thomasf10/cosy_cafeteria/Report/Onderzoek op sensoren.docx

# Eerste testen op de CCS811

- Eerste test: meting op 60 sec => meting niet meteen na slaap beschikbaar.
- Tweede test metingen 250 ms en 1s => me chronometer gechronometreerd ongeveer 1 second tussen elke meting. Verder nauwkeuriger onderzoek nodig. Tijd van de meting zelf niet de tijd tussen weergaven.
- Derde test 10 SEC => Eerste meting duurt precies langer dan de daarop volgende die zijn mooi consistent om de 10 seconden.
- Vierde test opmeten van 250ms => Eerst meting duurt ongeveer 940ms na uit slaap. Vanaf daarna effectief om de 250 ms een meting. => Dit is zeer consistent.

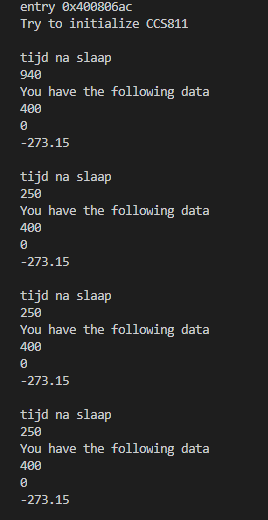
[picture p29: figure]

- Vijfde test 1 second nauwkeurig meten. Zelfde resultaat van eerste meting trager en volgende meting om de 250ms. Een meting mogelijk. Dit is achter elke meting dus. Eerste keer duurt het wel heel lang. Dit komt meteen achter initialisatie. Dus misschien intensiteit meting intensiever bij 250ms. Straks datasheet vermogen verbruik en uitleg bekijken.

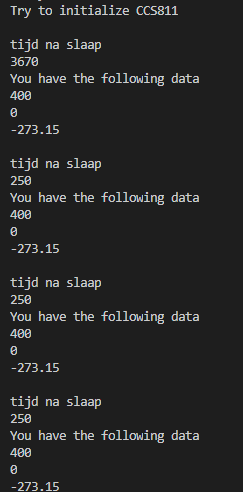
[picture p30: figure]

- Zesde test wat bij 10 seconden meting duurt dan ook 250ms? Antwoord nee, de meting duurt nu veel langer zelf 8,12 seconden. Meting snelheid 250ms en 1s zelfde maar interval tussen elke meting is verschillend. 250ms sneller inzetbaar na initialisatie of (lange slaap?).

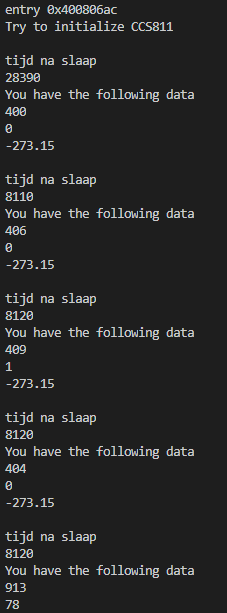
[picture p31: figure]

- Indien CCS811 vanuit idle wordt gestart duurt het altijd lang? Antwoor dis éénduidig ja, zowle voor de 250ms als voor de 1s. Dus dat omzetten van meetmethode kost extra tijd ook al komt hij uit idle. Beter gewoon in en uitslaap brengen werkt zeer snel enz al minder aan tijd kosten voor sensor basis verbruik. Ik zou ook opteren voor de 250msec in plaats van de 1s sneller een eerst resultaat waarschijnlijk na lange uitstand en dus ook sneller af zetten mogelijk. Verbruik is dezelfde bij beide. Tijdens de 250ms kunnen we effectief ook een andere meting / instelling doen van andere elementen.

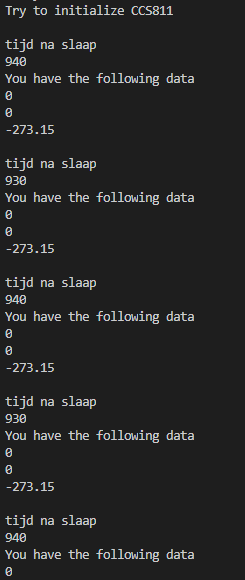
[picture p32: figure]

Bij effect van de snelle mode over een ganse minuut bekeken is bij continue meer verbruik maar dat zal gedurende 1 minuut zijn want dan voer je constant metingen uit en voed je de sensor continue. Bij deze impuls methode veel minder en dus sneller voeding afzetten. 1 ding nog testen op school. Is het verbruik komt dit wel ten goede is er een opstart stroompiek of niet?

Wat als we naar realistische verspreiding van metingen gaan.

- Meting om de 5 minuten:

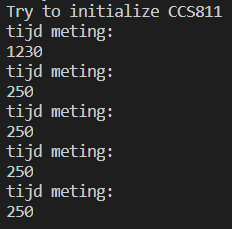
[picture p33: figure]

- Meting om het uur:

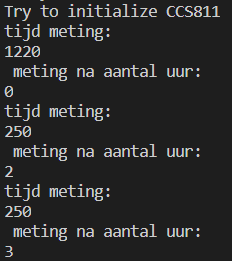
[picture p34: figure]

Indeed after a sleep time of 1hour the respons of the sensor is 250 ms.

Dus we kunnen eigenlijk deze tijd ook nuttig gebruiken we weten na 250ms na de CCS811 uit slaap te brengen dat hij een meting klaar heeft staan.

Mijn idee als dit ook bij de AMG zo is, zou ik een functie schrijven die eerst de traagste sensor activeert en dan de rest. Vanaf er een sensor data heeft die al uitlezen en weer in slaapbrengen. Enzo elke sensor afgaan tot we ze allemaal hebben uitgelezen en meteen in slaapgezet of voeding uit. Nu voor de CCS811 raad ik het afomdat zoals je ziet hij waarschijnlijk moet eerts geinitaliseerd worden en dan zijn eerste meting altijd toch wel 4x langer duurt.

# Gezamelijke testen op de AMG8833

Dit is het meest snelle resultaat, dit is vantoepassing indien we elke pixal van de AMG8833 sensor zouden uitmeten. Waarom eerst AMG dan CCS => CCS zakl pas na 250ms een resultaat hebben de AMG al na 105. Als de meting klaar is, kan je meteen de CCS uitlezen. Na de wake fucntie zal een delay van 105ms moeten gekozen worden. Ik ga ook nog de ADC er proberen in te steken en bekijken wat dan delays worden.

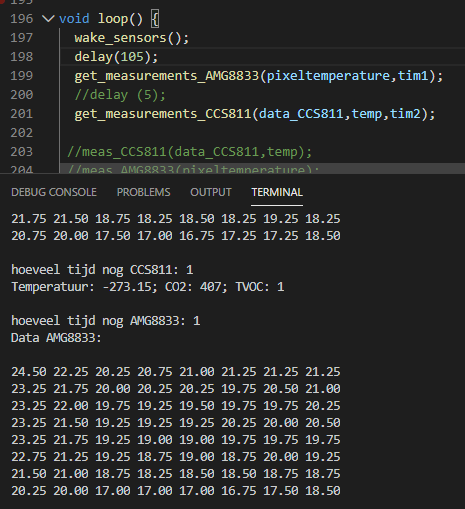
[picture p35: figure]

Na de ADC zal ik nog met de greco verbruiksmetingen doen en dan is dit verslag compleet.

The ADC was added, the ADC measurement did not introduced an extra delay. So, after the wake and ADC result there is a timeframe of 105 ms that we must wait for data of the AMG8833 and the CCS811 that will be even later available.

# Persoon detectie testen

## Hoogte 3,4m koude ruimte

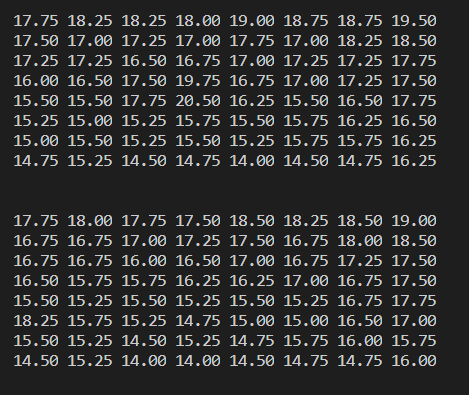
[picture p36: figure]

D

ZIe ook Excel, daarin zie je dat als de sensor op 3,4 meter hoog is een persoon door 1 à 2 pixels te Sherkenen en ligt in graden celcius drie graden hoger dan niet. Dit is wel in een koudere ruimte gebeurd zie vooral de temperaturen die zijn effectief zo laag.

Even nog een berekening doen checken of dat klopt. Verschil in hoogte is 1,6 m want ik ben zelf 1,8m ongeveer. Dus beetje geometrie nu doen.

30°

? m

1,7 m

tan 30°=(overstaande)/(aanliggende)=>overstaande=aanliggende∙tan30 °=1,6 m∙0,577=0,924m

Dit over vier pixels verspreid => 0,23 meter.

1 http://www.dinbelg.be/volwassenentotaal.htm

2 https://ohsonline.com/Articles/2008/01/Study-Womens-Skulls-Thicker-Mens-Wider-Might-Affect-Protection-Design.aspx

Dit is een tweede bron

Dus dit kan inderdaad wel goed kloppen. Weet ook we geven vooral langs ons hoofd veel warmte af als we ons kleden dus.

Bekijk ook het csv-bestand ‘Person tracking’. Daar zie me getracked worden door de de AMG sensor. Ik zette meestal ongeveer een halve meter een stap zijwaarts of voor-/achterwaards. Dus dat komt precies wel mooi uit met de resultaten.

## Metingen verschillende elementen

Eerst blok is op het hoofd gericht, tweede is borst met een dikke trui en tot slot iets van de omgeving. Dit laatste is wel op een meter afstand maar het is wel een goede represetatie van de warmte in de ruimte.

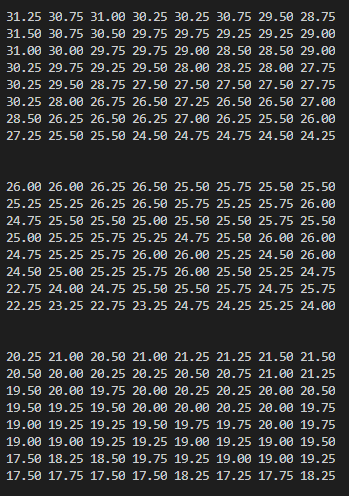
[picture p37: figure]

Laatste onderzoek is het verbruik nog, dit zal eerder voor volgend weekend zijn, denk ik.
