thomasf10/cosy_cafeteria/presentation/tussentijdsepresentatie.pptx

## Embedded 2 – Cosy cafetaria Corona presentation

By Tobias Cromheecke, Thomas Feys, Robin Van de Poel, Arthur Van den Storme
16-4-2020

## Index

- Power management
- Microcontroller + main PCB
- Sensor design
- Housing design
- Software design
- Wi-Fi communication
- Dashboard

## Power management

- Completed:

- Battery: Lithium-Ion battery
- Charger IC
- Protection IC
- Reverse polarity protection circtuit
- LDO: 3,7 V to 3,3 V
- Load switches to turn on/off the sensors
- Availability to measure current via wire to put a currentprobe on or sense resistor

- To do:

- Soldering
- Testing
- Designing revision

## Problems/limitations

- Delay times for deliveries due corona measures
- Lack of tools/instruments to solder and for testing:
  - Most power management IC’s have an exposed pad which needs a solder oven to solder properly
  - Lack of oscilloscope etc.

## Microcontroller + main PCB

- Completed:

- ESP32 single core
- Design main pcb
- Boot and reset button

- To do:

- Soldering
- Testing
- Designing revision

## Sensor design

- Completed:

- PCB design of separate sensor board
- Investigating response time of sensors
- Bringing sensors
  - Functions: init, get data, sleep,…

- To do:

- Power measurements
  - Checking measure mode is the most efficient
  - Checking with a Gecko development board

## Problems/limitations

- Correct cooperation of sensor board with the main board.

## Housing design

- Completed:

- Discussing a basic idea of the housing
- Getting the measurements of all available part
- A tutorial on 3D-printing design with fusion360

- To do:

- Design of the housing taken all the individual elements into account

## Problems/limitations

- Available 3D-printer
  - Do not own one
  - 3D-printer at work, could be a possibility Need to check with work
- Checking the fitting of the design in the housing

## Software design

- Completed:

- Entering and wakeup from deep sleep
- Save variables in RTC memory so that they are retained after deep sleep
- NTP synchronisation for time information => disable sensors at night

- To do:

- Put the individual pieces of software in one general structure
- Test the system
- Power measurements

## Problems/limitations

- No ability to fully disable sensors with load switch until the final PCB is ready
- No ability to measure power consumption
- Difficult to test full system because sensors, Raspberry Pi and ESP32-SOLO are not all available to one person

## Wi-Fi communication

- Completed:

- Data transfer between ESP32 and Python server
- Faster connection setup because of static IP => reduced power consumption

- To do:

- Process received data in Python
- Measure power consumption
- Test connection with actual sensor data instead of dummy data
- Test Python server on Raspberry Pi instead of laptop

## Dashboard

- Completed:

- Basic functionality for 1 type
- Data base design
- Data base implementation
- Functional heatmap

- To do:

- Test on raspberry pi
- Use real sensor data
- Make it look good
- Add the other sensors
- Main page
