thomasf10/cosy_cafeteria/Sensors/IR_Sensor_Embedded_Design_1_Verslag_Jona_Cappelle_Thomas_Feys.pdf

# Lab: Embedded system design 1

Thomas Feys | Jona Cappelle

16 december 2019

1

## Inhoudsopgave

1 Inleiding | 3
2 Sensor | 3
3 Systeem | 5
4 Code | 6
5 Power consumptie | 7
6 Besluit | 10
7 Bijlage | 11

2

## 1 Inleiding

Ons doel is om de wachtrij in de rabotaria te monitoren. Dit zullen we doen aan de hand van een IR grid sensor (AMG8833). Aan de hand van de uitgelezen waarden zullen we in het tweede semester bepalen hoeveel mensen er in de wachtrij staan. Deze informatie zullen we vervolgens via een app of website verspreiden.

## 2 Sensor

De sensor die we gebruiken om de wachtrij te monitoren is de AMG8833. Deze IR grid sensor heeft 8x8 pixels die de temperatuur weergeven. Volgens de datasheet kan a.d.h.v. de temperatuur een mens waargenomen worden vanop een afstand van 5 meter. De sensor kan gebruikt worden in 3 verschillende modes: normal, sleep en stand-by. In de normale mode heeft de sensor een verbruik van 4.5 mA. De stand-by mode heeft twee opties; de waardes kunnen geupdatet worden om de 60 ¨ seconden of om de 10 seconden. In deze mode is er een verbruik van 0.8 mA. Als laatste is er de sleep mode deze verbruikt 0.2 mA. Een overzicht van alle modes en de commando’s die verstuurd moeten worden om in deze modes te gaan, wordt weergegeven in figuur 1. Tijdens het testen van de sensor hebben we periodiek geswitched tussen de verschillende power modes. Het resultaat van deze test is te zien in figuur 2. De sensor heeft ook een interrupt pin. Deze pin geneert een interrupt als een van de pixels over of onder een bepaalde waarde gaat. Deze waarde is instelbaar.

3

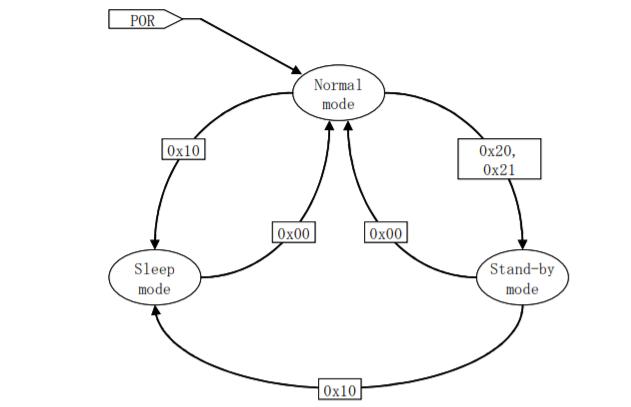
[picture p80: figure]

Figuur 1: Overzicht operating modes

4

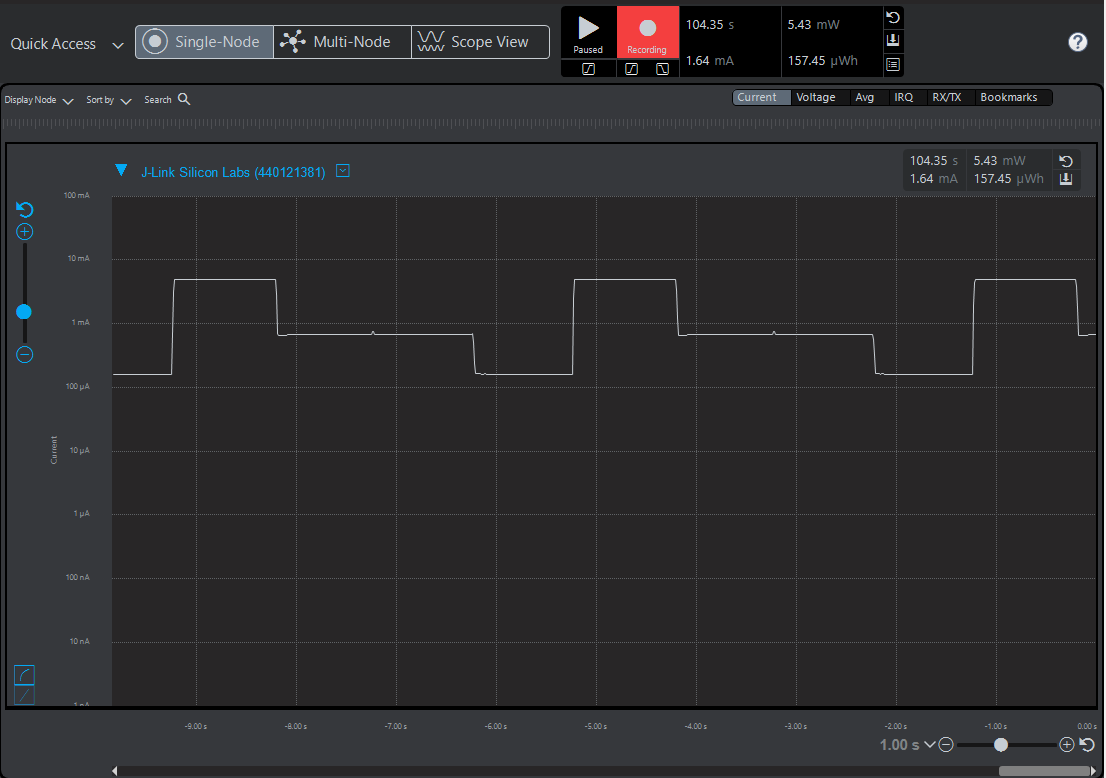
[picture p81: figure]

Figuur 2: Test van de verschillende powermodes

## 3 Systeem

### 3.1 Overzicht

De AMG8833 communiceert met de EFM32 via I2C. Naast de I2C communicatie is er ook een interrupt pin voorzien op de sensor. Deze pin genereert een interrupt als er een van de pixels een bepaalde, instelbare waarde overschrijdt. Een volledig overzicht van het systeem is te zien in figuur 3.

5

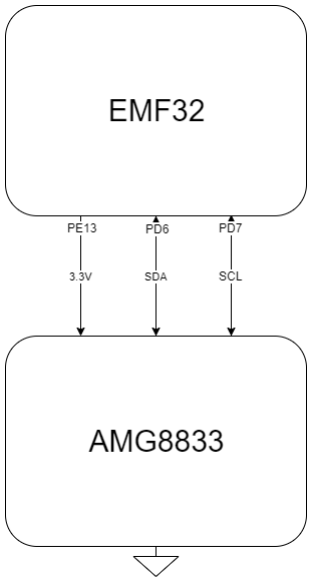
[picture p82: figure]

Figuur 3: Overzicht van het systeem

### 3.2 I2C

De communicatie met de sensor gebeurt via I2C. Het adres van de sensor is een 7 bit adres namelijk: 1101001. Aangezien we met een 7 bit adres zitten moet deze 1 bit geshift worden naar links. Dit adres moet telkens naar de sensor verstuurd worden vooraleer er iets gelezen of geschreven kan worden. De code die gebruikt wordt om de sensor uit te lezen, in andere powermodus te zetten en te interrupten wordt in de volgende sectie besproken.

## 4 Code

### 4.1 Functionaliteiten

Om gemakkelijk met de sensor te werken werd er een library geschreven voor de AMG8833. Er werden verschillende methodes geschreven om vlot te kunnen omgaan met de sensor. Er werd een functie geschreven om alle pixels uit te lezen. Naast de pixels is er ook een thermistor aanwezig in de sensor, ook hiervoor werd een functie geschreven. Er werden ook verschillende functies geschreven om makkelijk tussen de verschillende powermodes te kunnen wisselen. Een volledig overzicht van deze library en de rest van de code is terug te vinden op github: https://github.com/jonacappelle/Embedded_Project of in hoofdstuk 7.

6

### 4.2 Flow van de code

Aangezien de sensor in stand-by een verbruik van 0.8 mA heeft wordt deze altijd in sleep gezet. De sensor wordt om de 5 minuten uit sleep gehaald om alle pixels uit te lezen. Hierna wordt ze weer in sleep gezet. Een volledig overzicht van de code is terug te vinden in figuur 4.

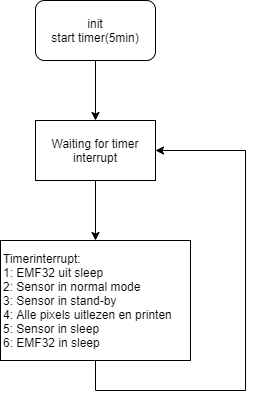
[picture p83: figure]

Figuur 4: flowchart van de code

## 5 Power consumptie

### 5.1 Sensor

De sensor heeft 3 verschillende powermodes, deze zijn te zien in figuur 5. Deze hebben we ook zelf opgemeten zoals te zien is in figuur 2. De gemeten waarden liggen in dezelfde grote orde als deze die opgegeven zijn in de datasheet, maar wijken toch een klein beetje af. In normal mode gebruikt onze sensor 4.95 mA, in stand-by 0.66 mA en in sleep 0.156 mA.

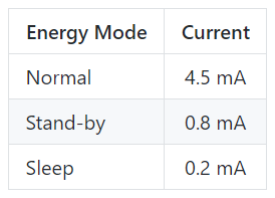
[picture p84: figure]

Figuur 5: powermodes van de sensor

7

### 5.2 Principe

Door de methode toe te passen die besproken werd in section 4.2 wordt de power consumptie sterk verminderd. De sensor zit enkel in stand-by tijdens het uilezen van de sensor waarde. De sensor zit ook 105 ms in normal mode, omdat je altijd naar de normal mode moet gaan als je uit sleep komt. Er werd een meting uitgevoerd om dit verbruik te controleren, dit is terug te vinden in figuur 6. Uit deze meting is te zien dat de sensor 105 ms in normal mode zit met een verbruik van 4.8 mA, 50ms in stand-by met een verbruik van 2.83 mA¹
en verder zit de sensor in sleep met een verbruik van 0.156 mA. Hierdoor bekomen we volgend verbruik per meting:

3.3 V ·

105 ms · 4.8 mA + 50 ms · 2.83 mA + 299.845 s · 0.156 mA = 156.4904 mJ/meting (1)

Een overzicht is te zien in tabel 1.

Power Mode | Verbruik [mA] | Tijd [s] | Energie [mJ]
Normal | 4.8 | 0.105 | 1.6632
Stand-By | 2.83 | 50 | 0.4669
Sleep | 0.156 | 299.845 | 154.3602
| | Totaal | 156.4904

Tabel 1: Verbruik voor ´e´en meting

Als we om de 5 minuten een meting uitvoeren, bekomen we volgend verbruik:

12 · 156.4904 mJ
| meting

= 1.877 mJ

| ⇒ 1.877 J
| 3600 s

= 0.52 mW

1Tijdens het uitlezen van de sensor ligt het verbruik hoger, hierdoor verbruikt de sensor 2.83 mA in stand-by ipv 0.8 mA

8

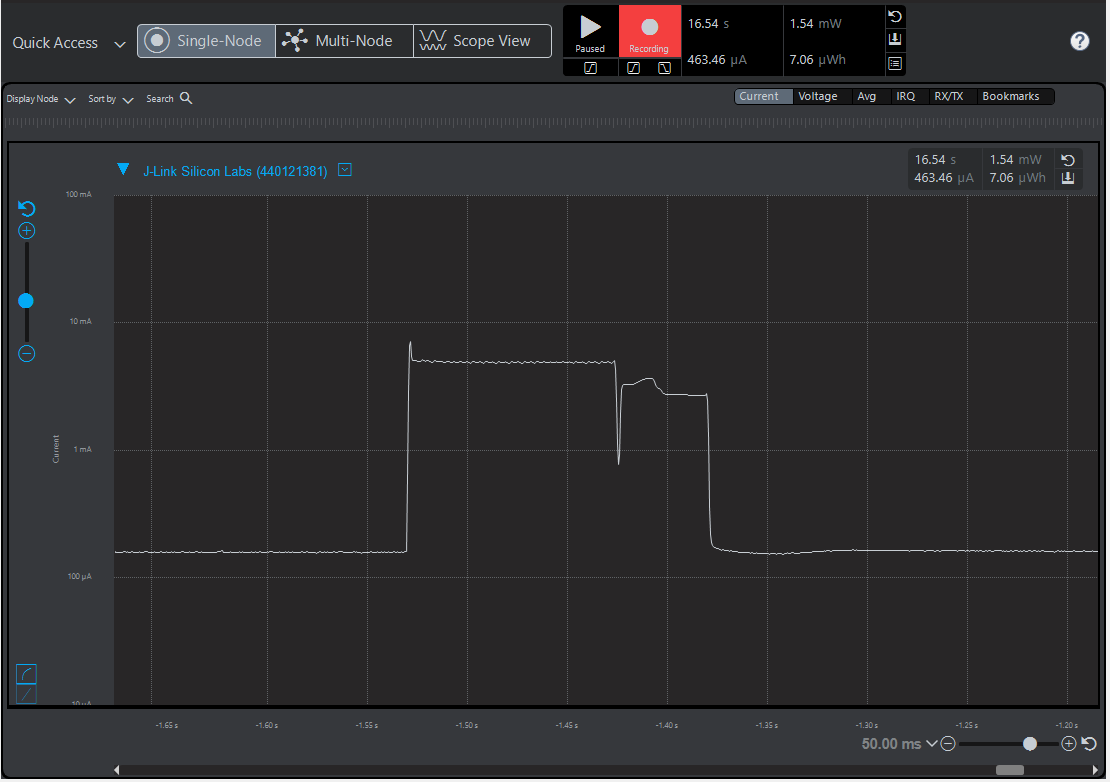
[picture p85: figure]

Figuur 6: Meting verbruik

9

## 6 Besluit

In dit labo hebben we een grid eye sensor aangesproken aan de hand van een I2C verbinding. Er werd een library geschreven om te werken met de verschillende functionaliteiten van de sensor. Deze library werd vervolgens gebruikt om de sensor op een low power manier te gebruiken. Dit leverde uiteindelijk een verbruik van 0.52 mW op.

10

## 7 Bijlage

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

44
45 | f l o a t r B u f f e r T h e rmi s t o r [ 1 ] ;
46 | f l o a t r B u f f e r P i x e l s [ 6 4 ] ;
47
48 | v o l a t i l e u i n t 3 2 t msTickCount ; | /∗ Counts 1ms t ime t i c k s ∗/
49 | s t a t i c v o l a t i l e u i n t 3 2 t msTicks ; /∗ c o u n t s 1ms t imeT ick s ∗/
50
51
52 | /∗ ∗∗∗∗∗∗∗∗∗∗∗∗∗∗∗∗∗∗∗∗∗∗∗∗∗∗∗∗∗∗∗∗∗∗∗∗∗∗∗∗∗∗∗∗∗∗∗∗∗∗∗∗∗∗∗∗∗∗∗∗∗∗∗∗∗∗∗∗∗∗∗∗ ∗/ /∗ ∗
53 | ∗ @ b r i e f
54 | ∗ | Sy sT ick H an dle r needed f o r t ime r f u n c t i o n a l i t y
55 | ∗
56 | ∗∗∗∗∗∗∗∗∗∗∗∗∗∗∗∗∗∗∗∗∗∗∗∗∗∗∗∗∗∗∗∗∗∗∗∗∗∗∗∗∗∗∗∗∗∗∗∗∗∗∗∗∗∗∗∗∗∗∗∗∗∗∗∗∗∗∗∗∗∗∗∗∗∗∗∗ ∗/
57 | void S y sTic k H andle r ( void )
58 | {
59 | msTicks++; | /∗ incremen t c o u n t e r n e c e s s a r y in Delay ( ) ∗/
60 | }
61
62 | /∗ ∗∗∗∗∗∗∗∗∗∗∗∗∗∗∗∗∗∗∗∗∗∗∗∗∗∗∗∗∗∗∗∗∗∗∗∗∗∗∗∗∗∗∗∗∗∗∗∗∗∗∗∗∗∗∗∗∗∗∗∗∗∗∗∗∗∗∗∗∗∗∗∗ ∗/ /∗ ∗
63 | ∗ @ b r i e f S y s T i c k D i s a b l e
64 | ∗ D i s a b l e s y s t i c k i n t e r r u p t s
65 | ∗∗∗∗∗∗∗∗∗∗∗∗∗∗∗∗∗∗∗∗∗∗∗∗∗∗∗∗∗∗∗∗∗∗∗∗∗∗∗∗∗∗∗∗∗∗∗∗∗∗∗∗∗∗∗∗∗∗∗∗∗∗∗∗∗∗∗∗∗∗∗∗∗∗∗∗ ∗/
66 | s t a t i c void S y sTi c kDi s a bl e ( void )
67 | {
68 | SysTick−>CTRL = 0 x0000000 ;
69 | }
70
71 | /∗ ∗∗∗∗∗∗∗∗∗∗∗∗∗∗∗∗∗∗∗∗∗∗∗∗∗∗∗∗∗∗∗∗∗∗∗∗∗∗∗∗∗∗∗∗∗∗∗∗∗∗∗∗∗∗∗∗∗∗∗∗∗∗∗∗∗∗∗∗∗∗∗∗ ∗/ /∗ ∗
72 | ∗ @ b r i e f
73 | ∗ | C on f ig u re t h e SysT ick t o use cmuClock CORE f o r 1 ms i n t e r r u p t s
74 | ∗
75 | ∗∗∗∗∗∗∗∗∗∗∗∗∗∗∗∗∗∗∗∗∗∗∗∗∗∗∗∗∗∗∗∗∗∗∗∗∗∗∗∗∗∗∗∗∗∗∗∗∗∗∗∗∗∗∗∗∗∗∗∗∗∗∗∗∗∗∗∗∗∗∗∗∗∗∗∗ ∗/
76 | void d e l a y i n i t ( void )
77 | {
78 | /∗ Se tup SysT ick Timer f o r 1 msec i n t e r r u p t s | ∗/
79 | i f ( S y sTi c k C o n fi g ( CMU ClockFreqGet ( cmuClock CORE ) / 1 0 0 0 ) ) {
80 | while ( 1 ) ;
81 | }
82 | }
83
84 | /∗ ∗∗∗∗∗∗∗∗∗∗∗∗∗∗∗∗∗∗∗∗∗∗∗∗∗∗∗∗∗∗∗∗∗∗∗∗∗∗∗∗∗∗∗∗∗∗∗∗∗∗∗∗∗∗∗∗∗∗∗∗∗∗∗∗∗∗∗∗∗∗∗∗ ∗/ /∗ ∗
85 | ∗ @ b r i e f
86 | ∗ | Non−low−power del ay , b u t non−b l o c k i n g
87 | ∗
88 | ∗ @param [ in ] d l y T i c k s
89 | ∗ | How many m i l l i sec on d s d e l a y

12

90 | ∗
91 | ∗∗∗∗∗∗∗∗∗∗∗∗∗∗∗∗∗∗∗∗∗∗∗∗∗∗∗∗∗∗∗∗∗∗∗∗∗∗∗∗∗∗∗∗∗∗∗∗∗∗∗∗∗∗∗∗∗∗∗∗∗∗∗∗∗∗∗∗∗∗∗∗∗∗∗∗ ∗/
92 | void d el a y ( u i n t 3 2 t dl yTi c k s )
93 | {
94 | | u i n t 3 2 t c u rTi c k s ;
95
96 | | c u rTi c k s = msTicks ;
97 | | while ( ( msTicks − c u rTi c k s ) < dl yTi c k s ) ;
98 | }
99
100 | /∗ ∗∗∗∗∗∗∗∗∗∗∗∗∗∗∗∗∗∗∗∗∗∗∗∗∗∗∗∗∗∗∗∗∗∗∗∗∗∗∗∗∗∗∗∗∗∗∗∗∗∗∗∗∗∗∗∗∗∗∗∗∗∗∗∗∗∗∗∗∗∗∗∗ ∗/ /∗ ∗
101 | ∗ @ b r i e f
102 | ∗ | C a l l b a c k f u n c t i o n f o r 5 min t ime r
103 | ∗
104 | ∗∗∗∗∗∗∗∗∗∗∗∗∗∗∗∗∗∗∗∗∗∗∗∗∗∗∗∗∗∗∗∗∗∗∗∗∗∗∗∗∗∗∗∗∗∗∗∗∗∗∗∗∗∗∗∗∗∗∗∗∗∗∗∗∗∗∗∗∗∗∗∗∗∗∗∗ ∗/
105 | void C all b a c k Sl e e p ( void )
106 | {
107 | | appS t a te = MEASURE;
108 | }
109
110
111 | /∗ ∗∗∗∗∗∗∗∗∗∗∗∗∗∗∗∗∗∗∗∗∗∗∗∗∗∗∗∗∗∗∗∗∗∗∗∗∗∗∗∗∗∗∗∗∗∗∗∗∗∗∗∗∗∗∗∗∗∗∗∗∗∗∗∗∗∗∗∗∗∗∗∗ ∗/ /∗ ∗
112 | ∗ @ b r i e f GPIO Even IRQ f o r p u s h b u t t o n s on even−numbered p i n s
113 | ∗∗∗∗∗∗∗∗∗∗∗∗∗∗∗∗∗∗∗∗∗∗∗∗∗∗∗∗∗∗∗∗∗∗∗∗∗∗∗∗∗∗∗∗∗∗∗∗∗∗∗∗∗∗∗∗∗∗∗∗∗∗∗∗∗∗∗∗∗∗∗∗∗∗∗∗ ∗/
114 | void GPIO EVEN IRQHandler ( void )
115 | {
116 | | // Cle a r a l l even p in i n t e r r u p t f l a g s
117 | | GPIO IntClear ( 0 x5555 ) ;
118 | | appS t a te = MEASURE;
119
120 #i f DEBUG DBPRINT == 1 /∗ DEBUG DBPRINT ∗/
121 | | d b p ri n t ( ” I n t e r r u p t f i r e d ! 1 ” ) ;
122 #end i f /∗ DEBUG DBPRINT ∗/
123 }
124
125 | /∗ ∗∗∗∗∗∗∗∗∗∗∗∗∗∗∗∗∗∗∗∗∗∗∗∗∗∗∗∗∗∗∗∗∗∗∗∗∗∗∗∗∗∗∗∗∗∗∗∗∗∗∗∗∗∗∗∗∗∗∗∗∗∗∗∗∗∗∗∗∗∗∗∗ ∗/ /∗ ∗
126 | ∗ @ b r i e f GPIO Odd IRQ f o r p u s h b u t t o n s on odd−numbered p i n s
127 | ∗∗∗∗∗∗∗∗∗∗∗∗∗∗∗∗∗∗∗∗∗∗∗∗∗∗∗∗∗∗∗∗∗∗∗∗∗∗∗∗∗∗∗∗∗∗∗∗∗∗∗∗∗∗∗∗∗∗∗∗∗∗∗∗∗∗∗∗∗∗∗∗∗∗∗∗ ∗/
128 | void GPIO ODD IRQHandler ( void )
129 | {
130 | | // Cle a r a l l odd p in i n t e r r u p t f l a g s
131 | | GPIO IntClear ( 0xAAAA) ;
132 | | appS t a te = MEASURE;
133
134 #i f DEBUG DBPRINT == 1 /∗ DEBUG DBPRINT ∗/
135 | | d b p ri n t ( ” I n t e r r u p t f i r e d ! 2 ” ) ;

13

136 #end i f /∗ DEBUG DBPRINT ∗/
137 }
138
139 | /∗ ∗∗∗∗∗∗∗∗∗∗∗∗∗∗∗∗∗∗∗∗∗∗∗∗∗∗∗∗∗∗∗∗∗∗∗∗∗∗∗∗∗∗∗∗∗∗∗∗∗∗∗∗∗∗∗∗∗∗∗∗∗∗∗∗∗∗∗∗∗∗∗∗ ∗/ /∗ ∗
140 | ∗ @ b r i e f
141 | ∗ | Main f u n c t i o n
142 | ∗
143 | ∗ @ d e t a i l s
144 | ∗ | We used a s t a t e machine t o c o n t r o l t h e s t a t e s where our m i c r o c o n t r o l l e r i s in
145 | ∗
146 | ∗∗∗∗∗∗∗∗∗∗∗∗∗∗∗∗∗∗∗∗∗∗∗∗∗∗∗∗∗∗∗∗∗∗∗∗∗∗∗∗∗∗∗∗∗∗∗∗∗∗∗∗∗∗∗∗∗∗∗∗∗∗∗∗∗∗∗∗∗∗∗∗∗∗∗∗ ∗/
147 | int main ( void )
148 | {
149 | /∗ I n f i n i t e l o o p ∗/
150 | while ( 1 )
151 | {
152 | switch ( appS t a te )
153 | {
154 | case INIT :
155 | {
156 | /∗ Chip e r r a t a ∗/
157 | CH IP Init ( ) ;
158
159 | /∗ Enable GPIO c l o c k s ∗/
160 | CMU ClockEnable ( cmuClock GPIO , t r u e ) ;
161 | CMU ClockEnable ( cmuClock HFPER , t r u e ) ; // Needed t o use GPIO
162 | CMU ClockEnable ( cmuClock CORE , t r u e ) ;
163
164 | /∗ Watchdog s e t u p − Use d e f a u l t s , e x c e p t s f o r t h e s e : ∗/
165 | w I ni t . em2Run = t r u e ;
166 | w I ni t . em3Run = t r u e ;
167 | w I ni t . p e r S el = wdogPeriod 4k ; /∗ 4k 1kHz p e r i o d s s h o ul d g i v e ˜4 | sec on d s in EM3 ∗/
168
169 | /∗ I n i t i a l i z e RTC t ime r . ∗/
170 | RTCDRV Init ( ) ;
171 | RTCDRV AllocateTimer ( &xTimerForWakeUp ) ;
172
173 | /∗ S t a r t I2C ∗/
174 | I I C I n i t ( ) ;
175
176 | /∗ S t a r t AMG8833 Temp s e n s o r ∗/
177 | AMG8833 Init ( ) ;
178
179 | /∗ S t a r t Delay ∗/
180 | d e l a y i n i t ( ) ;
181

14

182 | /∗ Se tup p r i n t i n g t o v i r t u a l COM p o r t ∗/
183 | #i f DEBUG DBPRINT == 1 /∗ DEBUG DBPRINT ∗/
184 | dbp rin t IN IT (USART1, 4 , t rue , f a l s e ) ;
185 | #e n d i f /∗ DEBUG DBPRINT ∗/
186
187 | appS t a te = MEASURE;
188 | } break ;
189 | case MEASURE:
190 | {
191 | /∗ Se t t o StandBy 10 s e c ∗/
192 | AMG8833 Sleep ( f a l s e ) ;
193 | AMG8833 StandBy ( STBY 60 ) ;
194
195 | RTCDRV StartTimer ( xTimerForWakeUp , rtcdrvTimerTypeOneshot , 1 0 5 , NULL, NULL ) ;
196 | EMU EnterEM2 ( t r u e ) ;
197
198 | //AMG8833 Thermistor Read ( r B u f f e r T h e rm i s t o r ) ;
199 | AMG8833 Pixels Read ( r B u f f e r P i x e l s ) ;
200
201 | appS t a te = SLEEP;
202
203 #i f DEBUG DBPRINT == 1 /∗ DEBUG DBPRINT ∗/
204 | AMG8833 Pixel Print ( r B u f f e r P i x e l s ) ;
205 #end i f /∗ DEBUG DBPRINT ∗/
206
207 | appS t a te = SLEEP;
208 | } break ;
209 | case SLEEP:
210 | {
211 | /∗ Sensor t o s l e e p −−> 0 . 2 mA ∗/
212 | AMG8833 Sleep ( t r u e ) ;
213
214 | /∗ EFM t o s l e e p ∗/
215 | S y sTi c kDi s a bl e ( ) ;
216 | RTCDRV StartTimer ( xTimerForWakeUp , rtcdrvTimerTypeOneshot , 5 0 0 0 , | C all b a c k Sl e e p , NULL ) ;
217 | EMU EnterEM2 ( t r u e ) ;
218 | } break ;
219 | }
220 | }
221 | }

15

../Embedded 1 AMG8833 Temp Sensor/AMG8833/AMG8833.h
1 | /∗
2 | ∗ AGM8833 . h
3 | ∗
4 | ∗ | Crea ted on : Nov 18 , 2019
5 | ∗ | Author : j on ac
6 | ∗/
7
8 | /∗ ∗∗∗∗∗∗∗∗∗∗∗∗∗∗∗∗∗∗∗∗∗∗∗∗∗∗∗∗∗∗∗∗∗∗∗∗∗∗∗∗∗∗∗∗∗∗∗∗∗∗∗∗∗∗∗∗∗∗∗∗∗∗∗∗∗∗∗∗∗∗∗∗∗ ∗/ /∗ ∗
9 | ∗ @ f i l e AMG8833 . h
10 | ∗ @ b r i e f I n t e r f a c e w i t h AMG8833 IR Temp camera
11 | ∗ @vers ion 1 . 0
12 | ∗ @author Jona C a p p ell e & Thomas Feys
13 | ∗ ∗∗∗∗∗∗∗∗∗∗∗∗∗∗∗∗∗∗∗∗∗∗∗∗∗∗∗∗∗∗∗∗∗∗∗∗∗∗∗∗∗∗∗∗∗∗∗∗∗∗∗∗∗∗∗∗∗∗∗∗∗∗∗∗∗∗∗∗∗∗∗∗∗∗∗ ∗/
14
15 #i fnd e f AMG8833 H
16 #def ine AMG8833 H
17
18 | /∗ Needed t o use u i n t x t ∗/
19 #include <s t d i n t . h> | /∗ Needed t o use u i n t x t ∗/
20 #include <s t d b o ol . h> | /∗ Needed t o use b o ol e a n s ∗/
21
22 #def ine I2C ADDRESS | ( 0 x69 << 1 ) /∗ MCU works w i t h | 10 b i t I2C a d d r e s s e s , so we need t o s h i f t our a d d r e s s 1 b i t ∗/
23
24 #def ine POWERCONTROL | 0 x00 | /∗ Power c o n t r o l a d d r e s s ∗/
25 #def ine POWERCONTROLNORMAL | 0 x00 | /∗ Power c o n t r o l s e t t o normal mode ∗/
26 #def ine POWER CONTROL SLEEP | 0 x10 | /∗ Power c o n t r o l s e t t o s l e e p mode ∗/
27 #def ine POWER CONTROL STBY 60 | 0 x20 | /∗ Power c o n t r o l s e t t o s t an dby , measure e v e ry 60 s e c ∗/
28 #def ine POWER CONTROL STBY 10 | 0 x21 | /∗ Power c o n t r o l s e t t o s t an dby , measure e v e ry 10 s e c ∗/
29
30 #def ine AMG8833 POWER PORT | gpioPortE | /∗ Power Por t ∗/
31 #def ine AMG8833 POWER PIN | 13 | /∗ Power Pin ∗/
32
33 #def ine AMG8833 INTERRUPT PORT | gpioPortD | /∗ I n t e r r u p t Por t ∗/
34 #def ine AMG8833 INTERRUPT PIN | 4 | /∗ I n t e r r u p t Pin ∗/
35 #def ine AMG8833 INT CONTROL REGISTER | 0 x03 | /∗ I n t e r r u p t c o n t r o l r e g i s t e r ∗/
36 #def ine AMG8833 INT LEVEL REGISTER | 0 x08 | /∗ I n t e r r u p t l e v e l r e g i s t e r ( upper l i m i t ) ∗/
37
38 #def ine RESET | 0 x01 | /∗ Rese t r e g i s t e r ∗/
39
40 #def ine THERMISTOR OUTPUT VALUE L | 0x0E | /∗ Beg in a d d r e s s o f t h e rm i s t o r o u t p u t ∗/
41
42 #def ine PIXEL 1 L | 0 x80 | /∗ Beg in a d d r e s s o f IR p i x e l a r r ay (128 r e g i s t e r s l o n g ) ∗/
43
44 #def ine THERMISTOR RES | 0. 0 6 2 5 | /∗ Cons tan t : t h e rm i s t o r r e s o l u t i o n ∗/
45 #def ine PIXEL RES | 0. 2 5 | /∗ Cons tan t : p i x e l r e s o l u t i o n ∗/

16

46
47 #def ine THRESHOLD VALUE | 20 | /∗ T h re s h ol d v a l u e f o r i n t e r r u p t ∗/
48
49 | /∗ SWITCH CASES ∗/
50 #def ine STBY 60 | 0 x00 | /∗ R e g i s t e r v a l u e t o s e t s tand−by | mode t o 60 s e c measurements ∗/
51 #def ine STBY 10 | 0 x01 | /∗ R e g i s t e r v a l u e t o s e t s tand−by | mode t o 10 s e c measurements ∗/
52
53 | void AMG8833 Init ( void ) ;
54 | void AMG8833 Thermistor Read ( f l o a t ∗ r B u f f e r T h e rmi s t o r ) ;
55 | void AMG8833 Pixels Read ( f l o a t ∗ r B u f f e r P i x e l s ) ;
56 | void AMG8833 Sleep ( b o ol e n a bl e ) ;
57 | void AMG8833 StandBy ( u i n t 8 t time ) ;
58 | void AMG8833 Reset ( void ) ;
59 | void AMG8833 Power ( b o ol e n a bl e ) ;
60 | void AMG8833 Interrupt ( b o ol e n a bl e ) ;
61
62 #end i f

17

../Embedded 1 AMG8833 Temp Sensor/AMG8833/AMG8833.c
1 | /∗
2 | ∗ AGM8833 . c
3 | ∗
4 | ∗ | Crea ted on : Nov 18 , 2019
5 | ∗ | Author : j on ac
6 | ∗/
7
8 | /∗ ∗∗∗∗∗∗∗∗∗∗∗∗∗∗∗∗∗∗∗∗∗∗∗∗∗∗∗∗∗∗∗∗∗∗∗∗∗∗∗∗∗∗∗∗∗∗∗∗∗∗∗∗∗∗∗∗∗∗∗∗∗∗∗∗∗∗∗∗∗∗∗∗∗ ∗/ /∗ ∗
9 | ∗ @ f i l e AMG8833 . c
10 | ∗ @ b r i e f I n t e r f a c e w i t h AMG8833 IR Temp camera
11 | ∗ @vers ion 1 . 0
12 | ∗ @author Jona C a p p ell e & Thomas Feys
13 | ∗ ∗∗∗∗∗∗∗∗∗∗∗∗∗∗∗∗∗∗∗∗∗∗∗∗∗∗∗∗∗∗∗∗∗∗∗∗∗∗∗∗∗∗∗∗∗∗∗∗∗∗∗∗∗∗∗∗∗∗∗∗∗∗∗∗∗∗∗∗∗∗∗∗∗∗∗ ∗/
14
15
16 #include ”AMG8833. h”
17 #include ” I2C . h”
18
19 /∗ d b p r i n t i n c l u d e ∗/
20 #include ” de bu g d bp ri n t . h” 21 #include ” em u s a r t . h”
22 #include ” em gpio . h”
23
24 /∗ Needed t o use u i n t x t ∗/ 25 #include <s t d i n t . h>
26 #include <s t d b o ol . h>
27
28
29 | /∗ ∗∗∗∗∗∗∗∗∗∗∗∗∗∗∗∗∗∗∗∗∗∗∗∗∗∗∗∗∗∗∗∗∗∗∗∗∗∗∗∗∗∗∗∗∗∗∗∗∗∗∗∗∗∗∗∗∗∗∗∗∗∗∗∗∗∗∗∗∗∗∗∗ ∗/ /∗ ∗
30 | ∗ @ b r i e f
31 | ∗ | Se tup AMG8833 Temperature s e n s o r
32 | ∗∗∗∗∗∗∗∗∗∗∗∗∗∗∗∗∗∗∗∗∗∗∗∗∗∗∗∗∗∗∗∗∗∗∗∗∗∗∗∗∗∗∗∗∗∗∗∗∗∗∗∗∗∗∗∗∗∗∗∗∗∗∗∗∗∗∗∗∗∗∗∗∗∗∗∗ ∗/
33 | void AMG8833 Init ( void )
34 | {
35 | | /∗ Se t t h e p in h i g h t o s u p pl y power t o t h e AMG8833 ∗/
36 | | GPIO PinModeSet (AMG8833 POWER PORT, AMG8833 POWER PIN, gpioModePushPull , 1 ) ;
37 | }
38
39 | /∗ ∗∗∗∗∗∗∗∗∗∗∗∗∗∗∗∗∗∗∗∗∗∗∗∗∗∗∗∗∗∗∗∗∗∗∗∗∗∗∗∗∗∗∗∗∗∗∗∗∗∗∗∗∗∗∗∗∗∗∗∗∗∗∗∗∗∗∗∗∗∗∗∗ ∗/ /∗ ∗
40 | ∗ @ b r i e f
41 | ∗ | Read t h e t h e rm i s t o r v a l u e o f t h e AMG8833 IR s e n s o r
42 | ∗ | The d a t a i s p r o c e s s e d as d e s c r i b e d in t h e d a t a s h e e t
43 | ∗
44 | ∗ @param [ in ] r B u f f e r T h e rm i s t o r
45 | ∗ | Address where t h e read t h e rm i s t o r v a l u e i s s t o r e d

18

46 | ∗
47 | ∗∗∗∗∗∗∗∗∗∗∗∗∗∗∗∗∗∗∗∗∗∗∗∗∗∗∗∗∗∗∗∗∗∗∗∗∗∗∗∗∗∗∗∗∗∗∗∗∗∗∗∗∗∗∗∗∗∗∗∗∗∗∗∗∗∗∗∗∗∗∗∗∗∗∗∗ ∗/
48 | void AMG8833 Thermistor Read ( f l o a t ∗ r B u f f e r T h e rmi s t o r )
49 | {
50 | | u i n t 8 t r B u f f e r [ 2 ] ;
51 | | u i n t 8 t wBu f fer [ 2 ] ;
52 | | wBu f fer [ 0 ] = THERMISTOR OUTPUT VALUE L;
53 | | wBu f fer [ 1 ] = 0 x00 ;
54
55 | | I IC W ri teRe adBu f fe r ( I2C ADDRESS, wBu f fer , 1 , r B u f f e r , 2 ) ;
56
57 | | ∗ r B u f f e r T h e rmi s t o r = ( ( r B u f f e r [ 1 ] << 8 ) | r B u f f e r [ 0 ] ) ∗ THERMISTOR RES;
58 | }
59
60
61 | /∗ ∗∗∗∗∗∗∗∗∗∗∗∗∗∗∗∗∗∗∗∗∗∗∗∗∗∗∗∗∗∗∗∗∗∗∗∗∗∗∗∗∗∗∗∗∗∗∗∗∗∗∗∗∗∗∗∗∗∗∗∗∗∗∗∗∗∗∗∗∗∗∗∗ ∗/ /∗ ∗
62 | ∗ @ b r i e f
63 | ∗ | Read t h e v a l u e o f a l l 64 IR p i x e l s
64 | ∗ | The d a t a i s p r o c e s s e d as d e s c r i b e d in t h e d a t a s h e e t
65 | ∗
66 | ∗ @param [ in ] r B u f f e r P i x e l s
67 | ∗ | Beg in a d d r e s s where t h e read v a l u e s o f t h e p i x e l a r r ay i s s t o r e d
68 | ∗
69 | ∗∗∗∗∗∗∗∗∗∗∗∗∗∗∗∗∗∗∗∗∗∗∗∗∗∗∗∗∗∗∗∗∗∗∗∗∗∗∗∗∗∗∗∗∗∗∗∗∗∗∗∗∗∗∗∗∗∗∗∗∗∗∗∗∗∗∗∗∗∗∗∗∗∗∗∗ ∗/
70 | void AMG8833 Pixels Read ( f l o a t ∗ r B u f f e r P i x e l s )
71 | {
72 | | u i n t 8 t r B u f f e r [ 1 2 8 ] ;
73 | | u i n t 8 t wBu f fer [ 2 ] ;
74 | | wBu f fer [ 0 ] = PIXEL 1 L ;
75 | | wBu f fer [ 1 ] = 0 x00 ;
76
77 | | I IC W ri teRe adBu f fe r ( I2C ADDRESS, wBu f fer , 1 , r B u f f e r , 1 2 8 );
78
79 | | for ( int i =0; i <64; i++)
80 | {
81 | | r B u f f e r P i x e l s [ i ] = ( ( r B u f f e r [ 2 ∗ i +1] << 8 ) | r B u f f e r [ 2 ∗ i ] ) ∗ PIXEL RES ;
82
83 | }
84 | }
85
86
87 | /∗ ∗∗∗∗∗∗∗∗∗∗∗∗∗∗∗∗∗∗∗∗∗∗∗∗∗∗∗∗∗∗∗∗∗∗∗∗∗∗∗∗∗∗∗∗∗∗∗∗∗∗∗∗∗∗∗∗∗∗∗∗∗∗∗∗∗∗∗∗∗∗∗∗ ∗/ /∗ ∗
88 | ∗ @ b r i e f
89 | ∗ | P r i n t a l l t h e v a l u e s o f t h e IR p i x e l a r r ay
90 | ∗
91 | ∗ @param [ in ] r B u f f e r P i x e l s

19

92 | ∗ | Address where t h e read t h e rm i s t o r v a l u e i s s t o r e d
93 | ∗
94 | ∗∗∗∗∗∗∗∗∗∗∗∗∗∗∗∗∗∗∗∗∗∗∗∗∗∗∗∗∗∗∗∗∗∗∗∗∗∗∗∗∗∗∗∗∗∗∗∗∗∗∗∗∗∗∗∗∗∗∗∗∗∗∗∗∗∗∗∗∗∗∗∗∗∗∗∗ ∗/
95 | void AMG8833 Pixel Print ( f l o a t ∗ r B u f f e r P i x e l s )
96 | {
97 #i f DEBUG DBPRINT == 1 /∗ DEBUG DBPRINT ∗/
98
99 | | for ( int j =0; j <8; j++)
100 | {
101 | | for ( int i =0; i <8; i++)
102 | | {
103 | | d b p ri n t I n t ( ( int ) r B u f f e r P i x e l s [ j ∗8+ i ] ) ;
104 | | d b p ri n t ( ” ” ) ;
105 | | }
106 | | d b p ri n tl n ( ” ” ) ;
107 | }
108 | | d b p ri n tl n ( ”−−−−−−−−−−−−−−−−−−−−−−−−−−−−−−−−−−−−−−−−−−−−−−−−−−−” ) ;
109
110 #end i f /∗ DEBUG DBPRINT ∗/
111 }
112
113
114 | /∗ ∗∗∗∗∗∗∗∗∗∗∗∗∗∗∗∗∗∗∗∗∗∗∗∗∗∗∗∗∗∗∗∗∗∗∗∗∗∗∗∗∗∗∗∗∗∗∗∗∗∗∗∗∗∗∗∗∗∗∗∗∗∗∗∗∗∗∗∗∗∗∗∗ ∗/ /∗ ∗
115 | ∗ @ b r i e f
116 | ∗ | Func t ion t o s e t t h e AMG8833 t o s l e e p
117 | ∗
118 | ∗ @ d e t a i l s
119 | ∗ | Power consump t ion s l e e p : 0 . 2 mA
120 | ∗
121 | ∗ @note
122 | ∗ | In s l e e p mode , n o t h i n g can be read from t h e r e g i s t e r s
123 | ∗
124 | ∗ @param [ in ] e n a bl e
125 | ∗ | @l i ’ t r u e ’ − s l e e p mode
126 | ∗ | @l i ’ f a l s e ’ − normal mode
127 | ∗
128 | ∗∗∗∗∗∗∗∗∗∗∗∗∗∗∗∗∗∗∗∗∗∗∗∗∗∗∗∗∗∗∗∗∗∗∗∗∗∗∗∗∗∗∗∗∗∗∗∗∗∗∗∗∗∗∗∗∗∗∗∗∗∗∗∗∗∗∗∗∗∗∗∗∗∗∗∗ ∗/
129 | void AMG8833 Sleep ( b o ol e n a bl e )
130 | {
131 | | u i n t 8 t r B u f f e r [ 1 ] ;
132 | | u i n t 8 t wBu f fer [ 2 ] ;
133 | | wBu f fer [ 0 ] = POWERCONTROL;
134
135 | | i f ( e n a bl e )
136 | {
137 | | wBu f fer [ 1 ] = POWER CONTROL SLEEP;

20

138 | | } e l s e {
139 | | wBu f fer [ 1 ] = POWER CONTROLNORMAL;
140 | }
141 | | I I C W ri t e B u f f e r ( I2C ADDRESS, wBu f fer , 2 ) ;
142
143 }
144
145
146 | /∗ ∗∗∗∗∗∗∗∗∗∗∗∗∗∗∗∗∗∗∗∗∗∗∗∗∗∗∗∗∗∗∗∗∗∗∗∗∗∗∗∗∗∗∗∗∗∗∗∗∗∗∗∗∗∗∗∗∗∗∗∗∗∗∗∗∗∗∗∗∗∗∗∗ ∗/ /∗ ∗
147 | ∗ @ b r i e f
148 | ∗ | Se t AGM8833 in s t an d by
149 | ∗
150 | ∗ @ d e t a i l s
151 | ∗ | Power consump t ion s tand−by : 0 . 8 mA
152 | ∗
153 | ∗ @note
154 | ∗ | Can ’ t go from SLEEP t o STAND−BY!
155 | ∗
156 | ∗ @param [ in ] t ime
157 | ∗ | @l i ‘STBY 10 ‘ − S e t s i n t e r v a l t o 10 s e c
158 | ∗ | @l i ‘STBY 60 ‘ − S e t s i n t e r v a l t o 60 s e c
159 | ∗∗∗∗∗∗∗∗∗∗∗∗∗∗∗∗∗∗∗∗∗∗∗∗∗∗∗∗∗∗∗∗∗∗∗∗∗∗∗∗∗∗∗∗∗∗∗∗∗∗∗∗∗∗∗∗∗∗∗∗∗∗∗∗∗∗∗∗∗∗∗∗∗∗∗∗ ∗/
160 | void AMG8833 StandBy ( u i n t 8 t time )
161 | {
162 | | u i n t 8 t wBu f fer [ 2 ] ;
163 | | wBu f fer [ 0 ] = POWERCONTROL;
164
165 | | switch ( time )
166 | {
167 | | case STBY 10 :
168 | | wBu f fer [ 1 ] = POWER CONTROL STBY 10;
169 | | break ;
170 | | case STBY 60 :
171 | | wBu f fer [ 1 ] = POWER CONTROL STBY 60;
172 | | break ;
173 | }
174
175 | | I I C W ri t e B u f f e r ( I2C ADDRESS, wBu f fer , 2 ) ;
176 | }
177
178 | /∗ ∗∗∗∗∗∗∗∗∗∗∗∗∗∗∗∗∗∗∗∗∗∗∗∗∗∗∗∗∗∗∗∗∗∗∗∗∗∗∗∗∗∗∗∗∗∗∗∗∗∗∗∗∗∗∗∗∗∗∗∗∗∗∗∗∗∗∗∗∗∗∗∗ ∗/ /∗ ∗
179 | ∗ @ b r i e f
180 | ∗ | Re se t s t h e AMG8833 s e n s o r t o d e f a u l t s e t t i n g s
181 | ∗
182 | ∗∗∗∗∗∗∗∗∗∗∗∗∗∗∗∗∗∗∗∗∗∗∗∗∗∗∗∗∗∗∗∗∗∗∗∗∗∗∗∗∗∗∗∗∗∗∗∗∗∗∗∗∗∗∗∗∗∗∗∗∗∗∗∗∗∗∗∗∗∗∗∗∗∗∗∗ ∗/
183 | void AMG8833 Reset ( void )

21

184 | {
185 | //TODO
186 | }
187
188 | /∗ ∗∗∗∗∗∗∗∗∗∗∗∗∗∗∗∗∗∗∗∗∗∗∗∗∗∗∗∗∗∗∗∗∗∗∗∗∗∗∗∗∗∗∗∗∗∗∗∗∗∗∗∗∗∗∗∗∗∗∗∗∗∗∗∗∗∗∗∗∗∗∗∗ ∗/ /∗ ∗
189 | ∗ @ b r i e f
190 | ∗ | Su p ply Power t o t h e AMG8833 VDD p in
191 | ∗
192 | ∗ @note
193 | ∗ | Needs t o be e n a bl e d f o r t h e s e n s o r t o work
194 | ∗
195 | ∗ @param [ in ] e n a bl e
196 | ∗ | @l i ’ t r u e ’ − Enable power
197 | ∗ | @l i ‘ f a l s e ’ − D i s a b l e power
198 | ∗∗∗∗∗∗∗∗∗∗∗∗∗∗∗∗∗∗∗∗∗∗∗∗∗∗∗∗∗∗∗∗∗∗∗∗∗∗∗∗∗∗∗∗∗∗∗∗∗∗∗∗∗∗∗∗∗∗∗∗∗∗∗∗∗∗∗∗∗∗∗∗∗∗∗∗ ∗/
199 | void AMG8833 Power ( b o ol e n a bl e )
200 | {
201 | i f ( e n a bl e )
202 | {
203 | GPIO PinOutSet (AMG8833 POWER PORT, AMG8833 POWER PIN ) ; /∗ Enable VDD p in ∗/
204 | } e l s e {
205 | GPIO PinOutClear (AMG8833 POWER PORT, AMG8833 POWER PIN ) ; /∗ D i s a b l e | VDD p in ∗/
206 | }
207 | }
208
209 | /∗ ∗∗∗∗∗∗∗∗∗∗∗∗∗∗∗∗∗∗∗∗∗∗∗∗∗∗∗∗∗∗∗∗∗∗∗∗∗∗∗∗∗∗∗∗∗∗∗∗∗∗∗∗∗∗∗∗∗∗∗∗∗∗∗∗∗∗∗∗∗∗∗∗ ∗/ /∗ ∗
210 | ∗ @ b r i e f
211 | ∗ | Sensor I n t e r r u p t f u n c t i o n a l i t y
212 | ∗
213 | ∗ @ d e t a i l s
214 | ∗ | @l i ’ b i t 0 ’ − INT o u t p u t a c t i v e
215 | ∗ | @l i ’ b i t 1 ’ − A b s ol u t e v a l u e i n t e r r u p t mode
216 | ∗
217 | ∗ @param [ in ] e n a bl e
218 | ∗ | @l i ’ t r u e ’ − Enable i n t e r r u p t s
219 | ∗ | @l i ‘ f a l s e ’ − D i s a b l e i n t e r r u p t s − o t h e r mode
220 | ∗∗∗∗∗∗∗∗∗∗∗∗∗∗∗∗∗∗∗∗∗∗∗∗∗∗∗∗∗∗∗∗∗∗∗∗∗∗∗∗∗∗∗∗∗∗∗∗∗∗∗∗∗∗∗∗∗∗∗∗∗∗∗∗∗∗∗∗∗∗∗∗∗∗∗∗ ∗/
221 | void AMG8833 Interrupt ( b o ol e n a bl e )
222 | {
223 | u i n t 8 t r B u f f e r [ 1 ] ;
224 | u i n t 8 t wBu f fer [ 2 ] ;
225 | wBu f fer [ 0 ] = AMG8833 INT CONTROL REGISTER;
226
227 | i f ( e n a bl e )
228 | {
229 | wBu f fer [ 1 ] = 0 x03 ;

22

230 | | } e l s e
231 | {
232 | | wBu f fer [ 1 ] = 0 x00 ;
233 | }
234
235 | | I IC W ri teRe adBu f fe r ( I2C ADDRESS, wBu f fer , 1 , r B u f f e r , 0 ) ;
236 | }
237
238 | /∗ ∗∗∗∗∗∗∗∗∗∗∗∗∗∗∗∗∗∗∗∗∗∗∗∗∗∗∗∗∗∗∗∗∗∗∗∗∗∗∗∗∗∗∗∗∗∗∗∗∗∗∗∗∗∗∗∗∗∗∗∗∗∗∗∗∗∗∗∗∗∗∗∗ ∗/ /∗ ∗
239 | ∗ @ b r i e f
240 | ∗ | Sensor I n t e r r u p t upper l i m i t s e t : TODO
241 | ∗
242 | ∗ @param [ in ] v a l u e
243 | ∗ | Upper l i m i t f o r i n t e r r u p t
244 | ∗∗∗∗∗∗∗∗∗∗∗∗∗∗∗∗∗∗∗∗∗∗∗∗∗∗∗∗∗∗∗∗∗∗∗∗∗∗∗∗∗∗∗∗∗∗∗∗∗∗∗∗∗∗∗∗∗∗∗∗∗∗∗∗∗∗∗∗∗∗∗∗∗∗∗∗ ∗/
245 | void AMG8833 Set Interrupt Upper Value ( int v al u e )
246 | {
247 | | u i n t 8 t r B u f f e r [ 1 ] ;
248 | | u i n t 8 t wBu f fer [ 2 ] ;
249 | | wBu f fer [ 0 ] = AMG8833 INT LEVEL REGISTER ;
250
251 | | u i n t 1 6 t temp ;
252
253 | | temp = ( u i n t 1 6 t ) ( v al u e / PIXEL RES ) ;
254
255 | | wBu f fer [ 1 ] = temp ;
256 | | //TODO
257
258 | | I IC W ri teRe adBu f fe r ( I2C ADDRESS, wBu f fer , 1 , r B u f f e r , 0 ) ;
259 | }

23
