thomasf10/cosy_cafeteria/Documentation/Power management design/Reverse polarity protection/Schematic.pdf

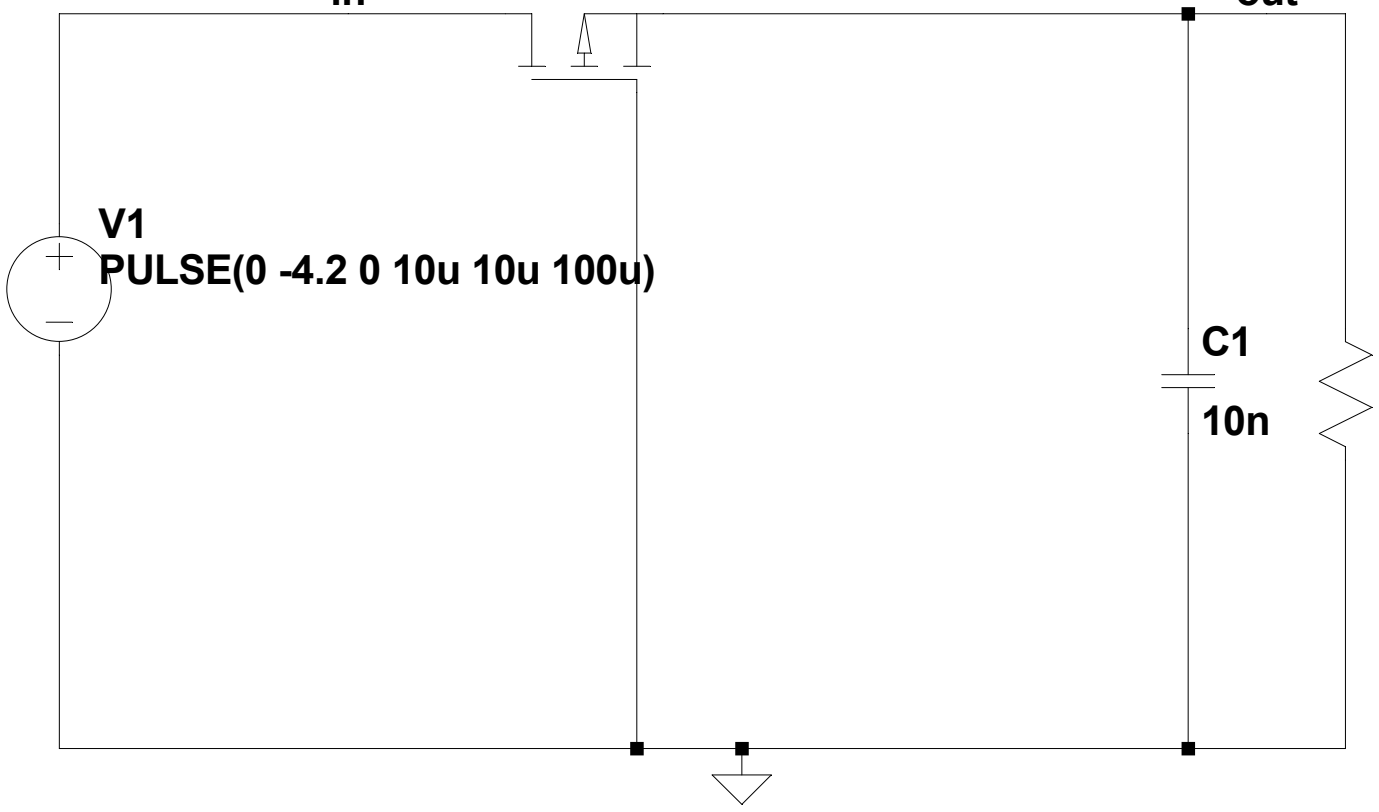
[picture p86: figure]
PULSE(0 -4.2 0 10u 10u 100u)

R2
10k
in | out U¹ ntr2101pt1

## .tran 0 300u 0

--- C:\Users\tobia\Documents\GitHub\cosy_cafeteria\Documentation\Power management design\Reverse polarity protection\Polarity_protection.asc ---
