thomasf10/cosy_cafeteria/Documentation/Power management design/Battery charging circuit/Calculations/BQ24075.pdf

# Calculations BQ24075

Tobias Cromheecke

March 6, 2020

## 1 Charging

Set CE low to initiate battery charging. The battery is charged in three phases:

1. Conditioning pre-charge
2. Constant current fast charge (current regulation)
3. Constant voltage tapering (voltage regulation)


Figure 1: Charge cycle

1

In the pre-charge phase, the battery is charged at with the pre-charge current IP RECHG. Once the battery voltage crosses the VLOW V threshold, the battery is charged with the fast-charge current ICHG. As the battery voltage reaches

VBAT(REG)

, the battery is held at a constant voltage of VBAT(REG) and the charge current tapers off as the battery approaches full charge. When the battery current reaches IT ERM, the CHG pin indicates charging done by going high-impedance.
The value of the fast-charge current is set by the resistor connected from the ISET pin to VSS, and is given by the equation:

ICHG =

KISET

RISET

The charge current limit is adjustable up to 1.5 A. The valid resistor range is 590 Ω to 8.9 kΩ. If ICHG is programmed as greater than the input current limit, the battery will not charge at the rate of ICHG, but at the slower rate of IIN(MAX) (minus the load current on the OUT pin, if any). In this case, the charger timers will be proportionately slowed down.

### 1.1 Charge Current Translator

When the charger is enabled, internal circuits generate a current proportional to the charge current at the ISET input. The current out of ISET is 1/400 (±10%) of the charge current. This current, when applied to the external charge current programming resistor, RISET , generates an analog voltage that can be monitored by an external host to calculate the current sourced from BAT.

VISET =

ICHG
400

RISET

## 2 System enable input

Connect SYSOFF high to turn off the FET connecting the battery to the system output. When an adapter is connected, charging is also disabled. Connect SYSOFF low for normal operation. SYSOFF is internally pulled up to VBAT through a large resistor (approximately 5 MΩ). Do not leave SYSOFF unconnected to ensure proper operation.

## 3 Calculations

### 3.1 Program the Fast Charge Current ICHG

RISET =

KISET

ICHG

From the electrical table we can find:

KISET = 890AΩ

2

The charge current limit is adjustable up to 1.5 A. The maximum charge current for the Panasonic NCR18650B battery is 1625 mA. Set the charge current to 1.3 A to have some margin for the battery lifetime.

RILIM =

890AΩ
1.3A

= 684.62Ω ≈ 680Ω

The valid resistor range is 590 Ω to 8.9 kΩ. Select the closest standard value, which for this case is 680 Ω. Connect this resistor between ISET (pin 16) and VSS.
ICHG =

890AΩ
680Ω = 1.31A

### 3.2 Program the Input Current Limit ILIM

RILIM =

KILIM

IIN(MAX)

From the electrical table we can find:

KILIM = 1610AΩ

The input current limit is adjustable up to 1.5 A. Set the input current limit higher than the charge current of 1.3 A.

RILIM =

1610AΩ
1.5A

= 1.073kΩ ≈ 1.1kΩ

The valid resistor range is 1.1 kΩ to 8 kΩ. Select the closest standard value, which for this case is 1.1 kΩ. Connect this resistor between ILIM (pin 12) and VSS.

IILIM =

1610AΩ
1.1kΩ

= 1.46A

### 3.3 Fast-Charge Safety Timer (TMR)

Leave TMR open to set to default safety timers. Connect to VSS to disable safety timers.

### 3.4 TS function

Connect a 10 kΩ resistor from TS to VSS to set the TS voltage at a valid level and maintain charging.

### 3.5 Selecting IN, OUT, and BAT Pin Capacitors

In most applications, all that is needed is a high-frequency decoupling capacitor (ceramic) on the power pin, input, output and battery pins. Using the values shown on the application diagram, is recommended. After evaluation of these

3

voltage signals with real system operational conditions, one can determine if capacitance values can be adjusted toward the minimum recommended values (DC load application) or higher values for fast high amplitude pulsed load applications. Note if designed high input voltage sources (bad adaptors or wrong adaptors), the capacitor needs to be rated appropriately. Ceramic capacitors are tested to 2x their rated values so a 16-V capacitor may be adequate for a 30-V transient (verify tested rating with capacitor manufacturer).

### 3.6 Selecting MOSFETs

Discharge Overcurrent Detection (OCD) voltage = 100 mV. RDSON = 30mΩ@VGS = 4.5V Maximum operating discharge current = 100mV
2∗30mΩ = 1.67A

4
