thomasf10/cosy_cafeteria/Report/fig/Transient_response_negative_input_pulse-eps-converted-to.pdf

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

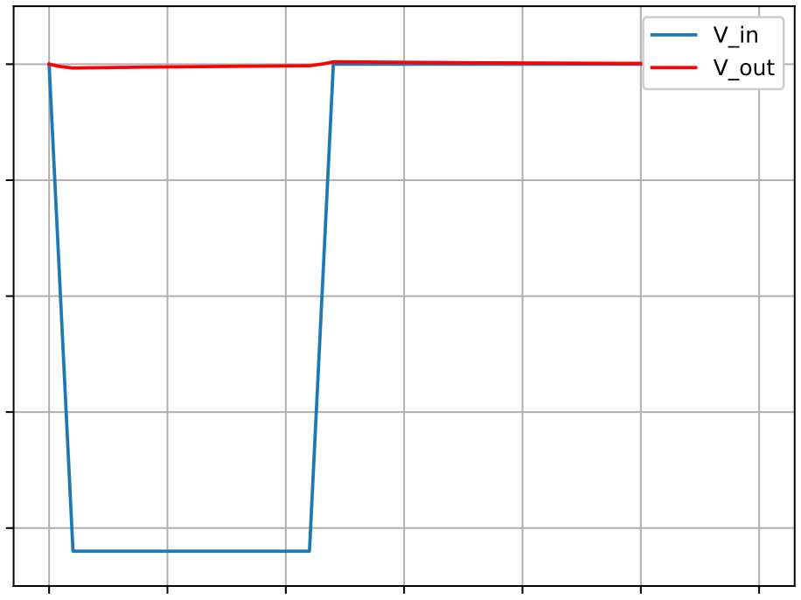
[picture p102: figure]
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
