thomasf10/cosy_cafeteria/Dashboard/img/cafetaria.jpg

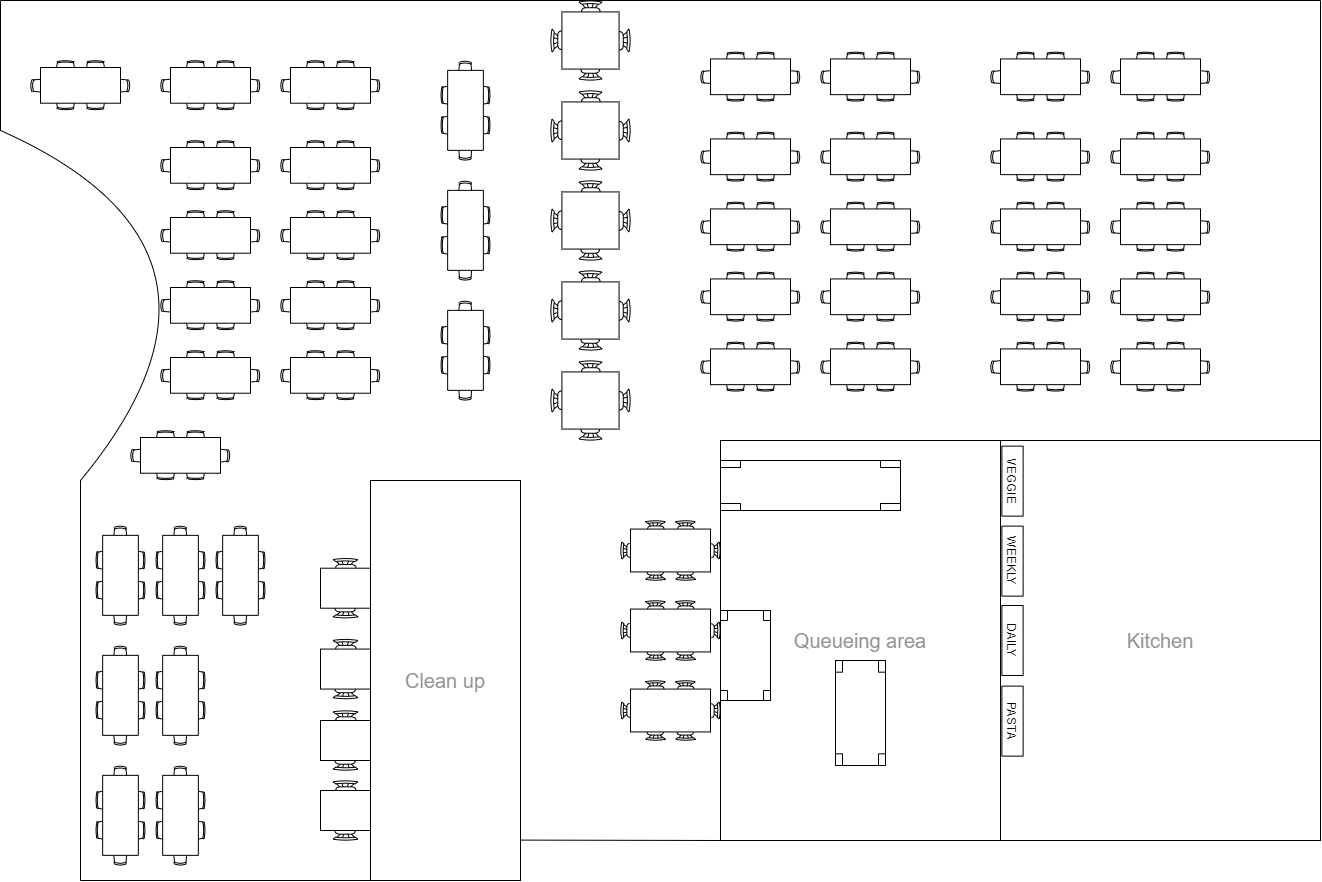
Dashboard/img/cafetaria.jpg
