thomasf10/cosy_cafeteria/Report/fig/TPS22919_principeschema.PNG

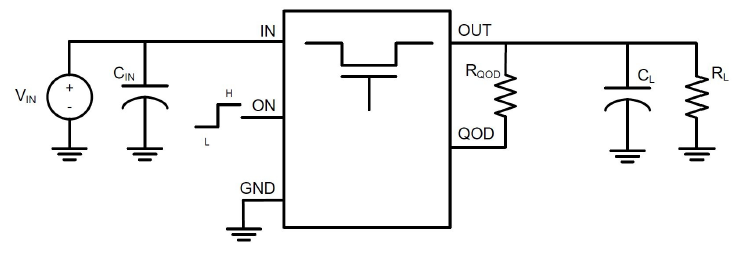
Report/fig/TPS22919_principeschema.PNG
