thomasf10/cosy_cafeteria/Wi-Fi/metingen_stroomprobe/metstroomprobe/1e_meting_start_in_loop_dan_sleep.PNG

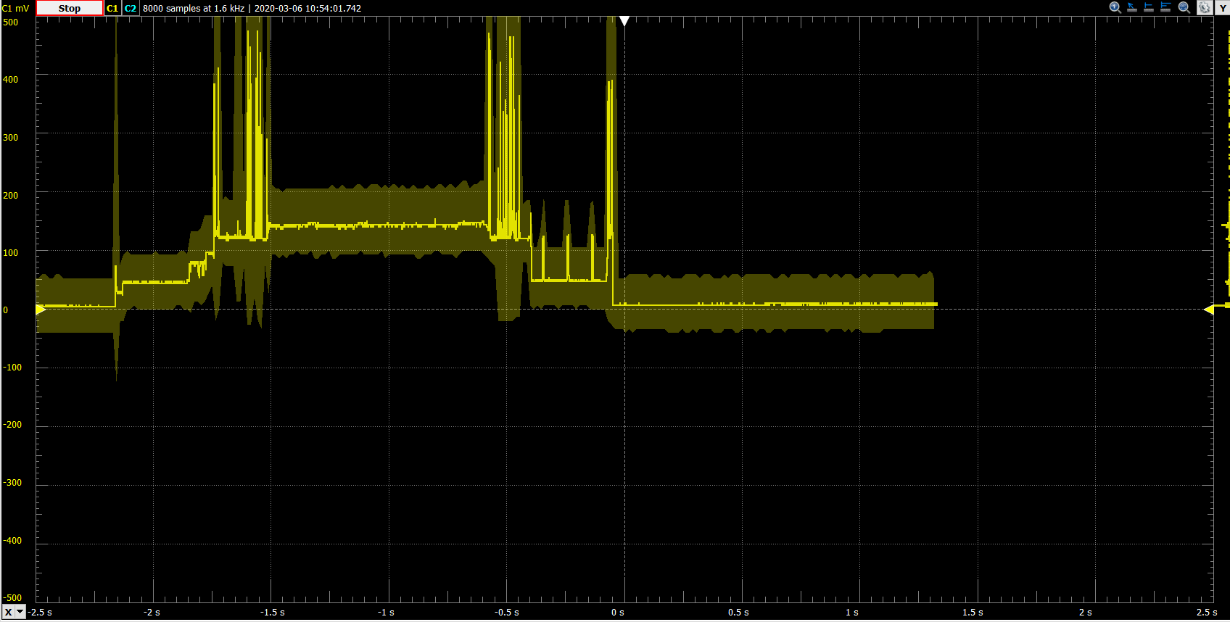
Wi-Fi/metingen_stroomprobe/metstroomprobe/1e_meting_start_in_loop_dan_sleep.PNG
