thomasf10/cosy_cafeteria/Wi-Fi/metingen_stroomprobe/metstroomprobe/2emeting_64_ints+string_doorsturen.png

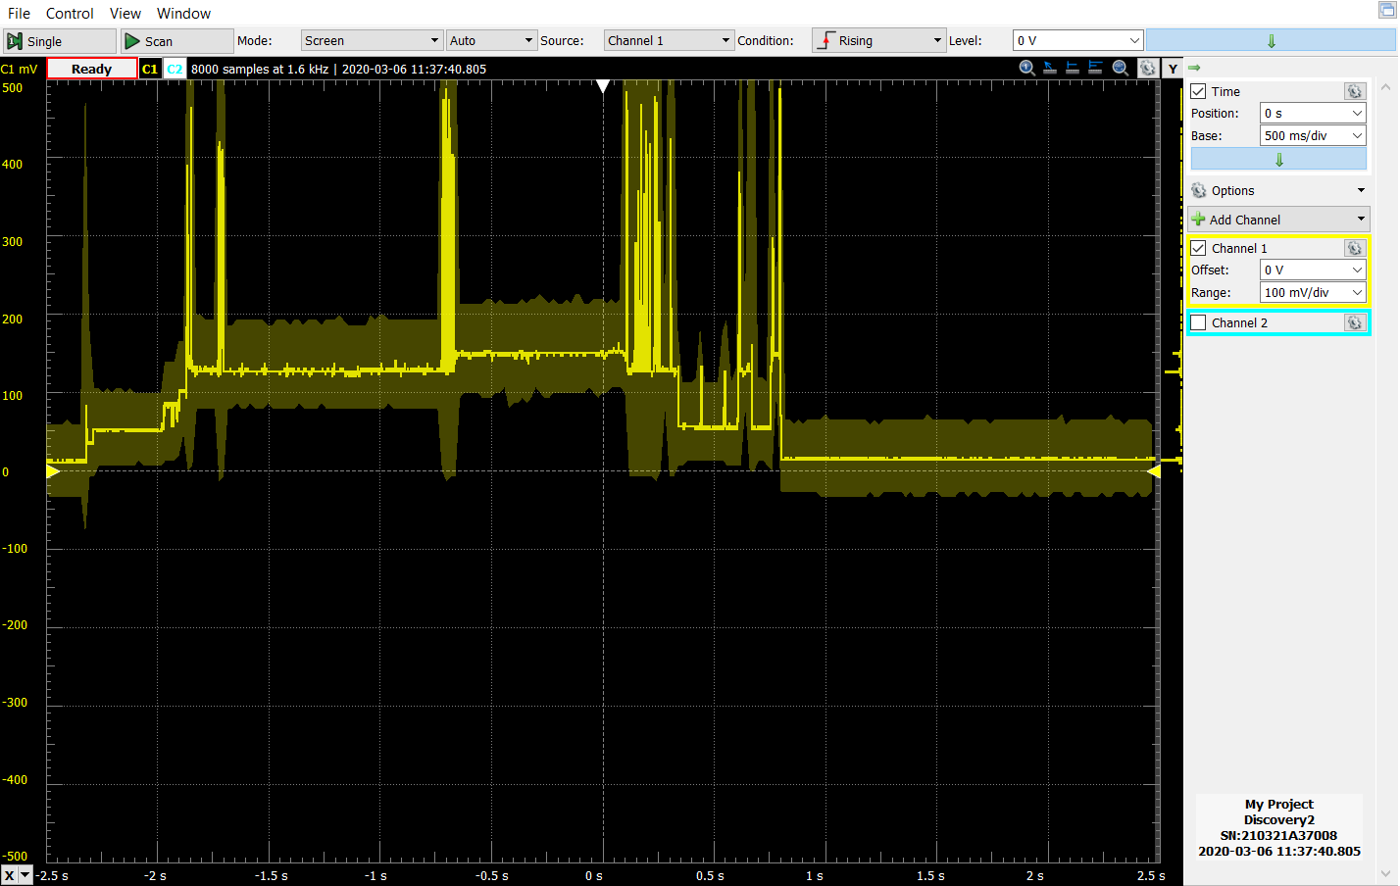
Wi-Fi/metingen_stroomprobe/metstroomprobe/2emeting_64_ints+string_doorsturen.png
