thomasf10/cosy_cafeteria/Wi-Fi/metingen_stroomprobe/metstroomprobe/3emeting_10_20_40_80_160Mhz.png

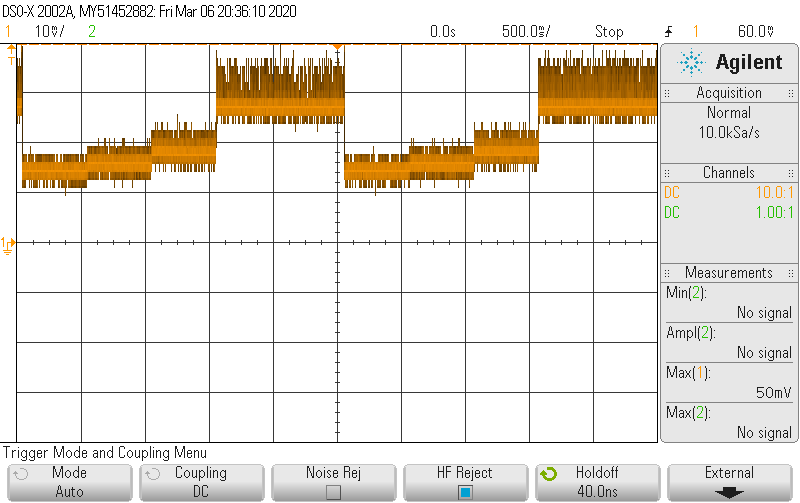
Wi-Fi/metingen_stroomprobe/metstroomprobe/3emeting_10_20_40_80_160Mhz.png
