thomasf10/cosy_cafeteria/Wi-Fi/metingen_stroomprobe/metstroomprobe/4e_meting_code_met_functie.png

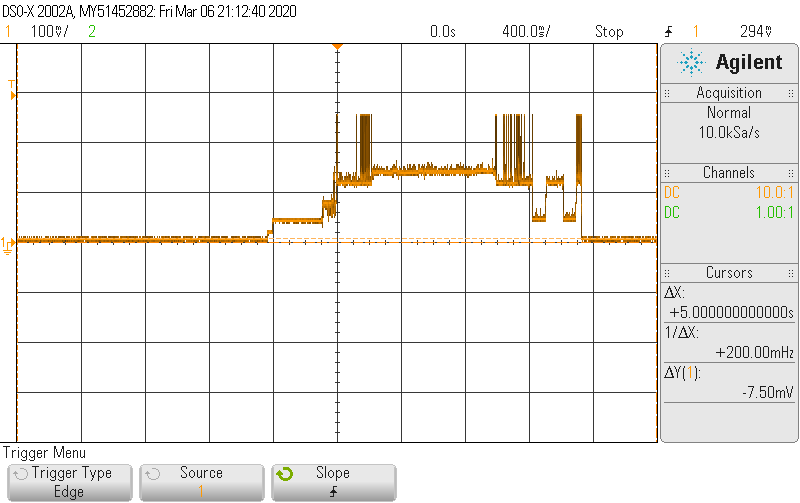
Wi-Fi/metingen_stroomprobe/metstroomprobe/4e_meting_code_met_functie.png
