thomasf10/cosy_cafeteria/Wi-Fi/power_esp8266.PNG

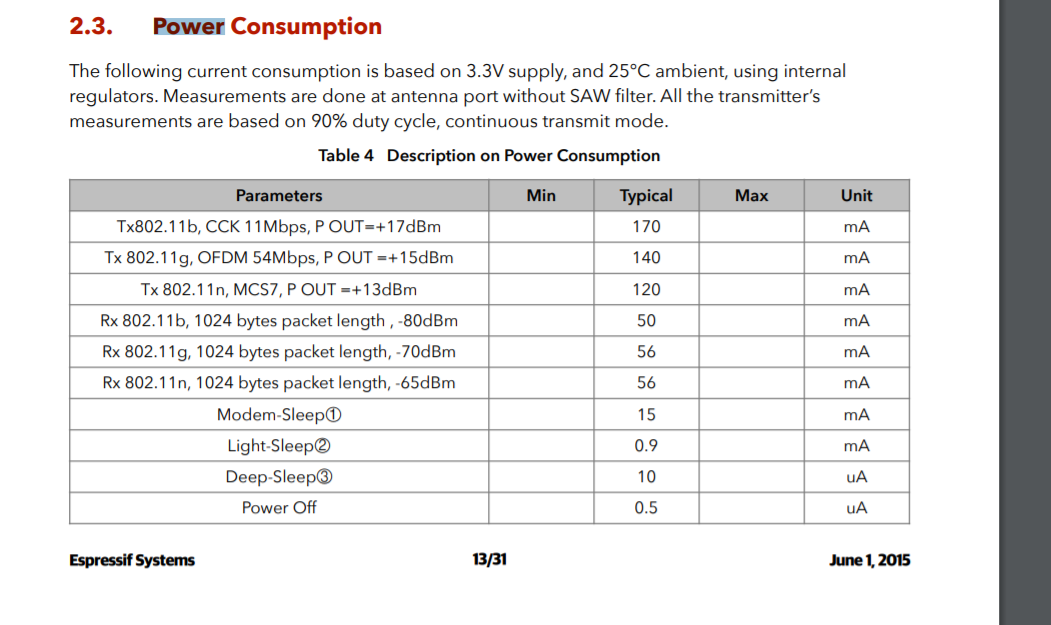
Wi-Fi/power_esp8266.PNG
