thomasf10/cosy_cafeteria/Wi-Fi/pwresp32.PNG

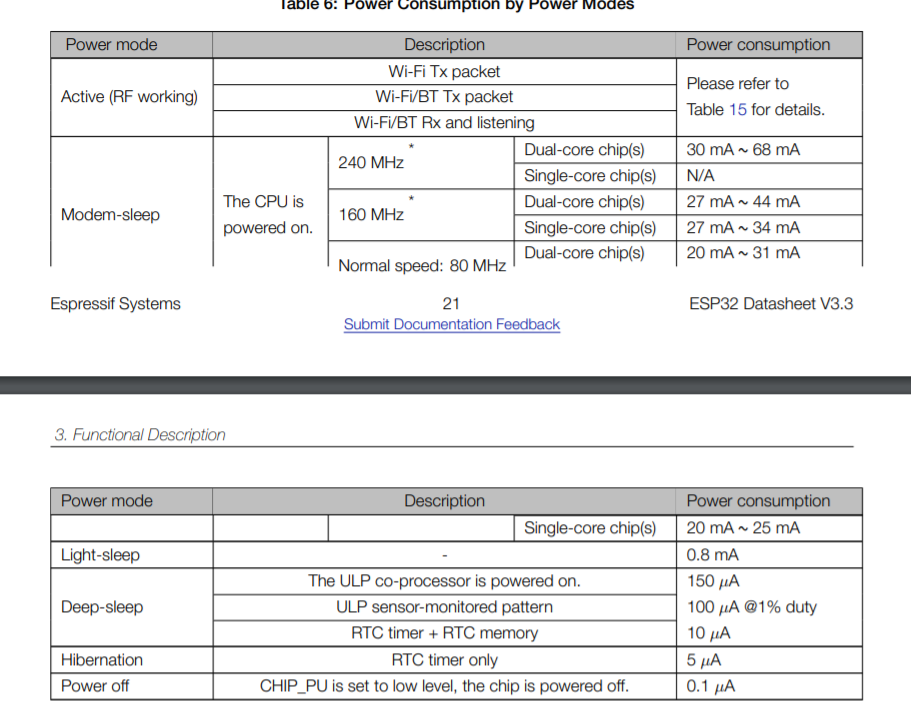
Wi-Fi/pwresp32.PNG
