thomasf10/cosy_cafeteria/powermeasurement/wifi/NO_static_ip_64ints.csv

#Digilent WaveForms Oscilloscope Acquisition
#Device Name: Discovery2
#Serial Number: SN:210321A4216E
#Date Time: 2020-04-19 17:12:53.201
#Sample rate: 1600Hz
#Samples: 8000
#Trigger: Source: Channel 1 Type: Edge Condition: Rising Level: 0 V Hyst.: Auto HoldOff: 0 s
#Channel 1: Range: 50 mV/div Offset: -240 mV
#Power Supplies: OFF
#Positive Supply: Rdy
#Voltage: 1 V
#Negative Supply: Rdy
#Voltage: -1 V
Time (s) | Channel 1 (V)
-2.1 | -0.000618286
-2.09937 | -0.000618286
-2.09875 | -0.000952086
-2.09813 | -0.00128588
-2.0975 | -0.00128588
-2.09687 | -0.000952086
-2.09625 | 4.93E-05
-2.09563 | 0.000383111
-2.095 | 0.00205211
-2.09437 | 0.00171831
-2.09375 | 0.00071691
-2.09312 | -0.000284487
-2.0925 | -0.00161968
-2.09187 | -0.00228728
-2.09125 | -0.00262108
-2.09062 | -0.00295488
-2.09 | -0.00262108
-2.08937 | -0.000284487
-2.08875 | -0.000952086
-2.08812 | -0.000952086
-2.0875 | -0.00128588
-2.08688 | -0.00295488
-2.08625 | -0.00395628
-2.08562 | -0.00362248
-2.085 | -0.00362248
-2.08438 | -0.00295488
-2.08375 | -0.00262108
-2.08312 | -0.00262108
-2.0825 | 4.93E-05
-2.08187 | 0.000383111
-2.08125 | 0.00071691
-2.08062 | 0.000383111
-2.08 | -0.000618286
-2.07937 | -0.000952086
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
