thomasf10/cosy_cafeteria/powermeasurement/wifi/NO_static_ip_64ints_2e_meting.csv

#Digilent WaveForms Oscilloscope Acquisition
#Device Name: Discovery2
#Serial Number: SN:210321A4216E
#Date Time: 2020-04-19 17:12:11.810
#Sample rate: 1600Hz
#Samples: 7575
#Trigger: Source: Channel 1 Type: Edge Condition: Rising Level: 0 V Hyst.: Auto HoldOff: 0 s
#Channel 1: Range: 50 mV/div Offset: -240 mV
#Power Supplies: OFF
#Positive Supply: Rdy
#Voltage: 1 V
#Negative Supply: Rdy
#Voltage: -1 V
Time (s) | Channel 1 (V)
-1.25 | 0.00205211
-1.24938 | 0.00171831
-1.24875 | 0.00138451
-1.24813 | 0.00171831
-1.2475 | 0.0040549
-1.24688 | 0.0033873
-1.24625 | 0.0030535
-1.24563 | 0.0030535
-1.245 | 0.00105071
-1.24438 | 0.000383111
-1.24375 | 0.00071691
-1.24313 | 0.00071691
-1.2425 | 0.00105071
-1.24188 | 0.00138451
-1.24125 | 0.00205211
-1.24063 | 0.0043887
-1.24 | 0.0047225
-1.23938 | 0.0047225
-1.23875 | 0.0043887
-1.23813 | 0.0033873
-1.2375 | 0.0033873
-1.23688 | 0.0030535
-1.23625 | 0.0030535
-1.23563 | 0.0030535
-1.235 | 0.0033873
-1.23438 | 0.0043887
-1.23375 | 0.0047225
-1.23313 | 0.0063915
-1.2325 | 0.0060577
-1.23188 | 0.0047225
-1.23125 | 0.0033873
-1.23063 | 0.00238591
-1.23 | 0.00205211
-1.22938 | 0.00171831
-1.22875 | 0.00138451
-1.22813 | 0.00171831
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
