thomasf10/cosy_cafeteria/powermeasurement/wifi/meting_all_sensorvalues.csv

#Digilent WaveForms Oscilloscope Acquisition
#Device Name: Discovery2
#Serial Number: SN:210321A4216E
#Date Time: 2020-04-24 14:11:29.461
#Sample rate: 800Hz
#Samples: 7505
#Trigger: Source: Channel 1 Type: Edge Condition: Rising Level: 0 V Hyst.: Auto HoldOff: 0 s
#Channel 1: Range: 50 mV/div Offset: -200 mV
Time (s) | Channel 1 (V)
-5 | 0.0693745
-4.99875 | -0.00205855
-4.9975 | -0.00305994
-4.99625 | -0.00239234
-4.995 | -0.00172475
-4.99375 | 0.000611848
-4.9925 | 0.000278049
-4.99125 | -0.00038955
-4.99 | -0.000723349
-4.98875 | -0.000723349
-4.9875 | 0.000611848
-4.98625 | 0.00161325
-4.985 | -0.00038955
-4.98375 | -0.00205855
-4.9825 | -0.00272614
-4.98125 | -0.000723349
-4.98 | -0.00105715
-4.97875 | -0.00205855
-4.9775 | -0.00305994
-4.97625 | -0.00272614
-4.975 | -0.00172475
-4.97375 | 0.000611848
-4.9725 | 0.000278049
-4.97125 | -0.00038955
-4.97 | -0.000723349
-4.96875 | -0.000723349
-4.9675 | 0.000611848
-4.96625 | 0.00161325
-4.965 | -0.00038955
-4.96375 | -0.00205855
-4.9625 | -0.00272614
-4.96125 | -0.000723349
-4.96 | -0.00105715
-4.95875 | -0.00205855
-4.9575 | -0.00305994
-4.95625 | -0.00272614
-4.955 | -0.00172475
-4.95375 | 0.000611848
-4.9525 | 0.000278049
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
