thomasf10/cosy_cafeteria/powermeasurement/wifi/meting_all_sensorvalues_2.csv

#Digilent WaveForms Oscilloscope Acquisition
#Device Name: Discovery2
#Serial Number: SN:210321A4216E
#Date Time: 2020-04-24 14:13:55.219
#Sample rate: 800Hz
#Samples: 5548
#Trigger: Source: Channel 1 Type: Edge Condition: Rising Level: 0 V Hyst.: Auto HoldOff: 0 s
#Channel 1: Range: 50 mV/div Offset: -200 mV
Time (s) | Channel 1 (V)
-5 | 0.00828923
-4.99875 | 0.00161325
-4.9975 | 0.00294844
-4.99625 | 0.00461744
-4.995 | 0.00394984
-4.99375 | 0.00361604
-4.9925 | 0.00328224
-4.99125 | 0.00394984
-4.99 | 0.00595263
-4.98875 | 0.00528504
-4.9875 | 0.00328224
-4.98625 | 0.00194704
-4.985 | 0.00161325
-4.98375 | 0.00361604
-4.9825 | 0.00328224
-4.98125 | 0.00127945
-4.98 | 0.000945647
-4.97875 | 0.00161325
-4.9775 | 0.00294844
-4.97625 | 0.00461744
-4.975 | 0.00394984
-4.97375 | 0.00361604
-4.9725 | 0.00328224
-4.97125 | 0.00394984
-4.97 | 0.00595263
-4.96875 | 0.00561884
-4.9675 | 0.00328224
-4.96625 | 0.00194704
-4.965 | 0.00127945
-4.96375 | 0.00361604
-4.9625 | 0.00328224
-4.96125 | 0.00127945
-4.96 | 0.000945647
-4.95875 | 0.00161325
-4.9575 | 0.00294844
-4.95625 | 0.00461744
-4.955 | 0.00394984
-4.95375 | 0.00361604
-4.9525 | 0.00328224
-4.95125 | 0.00394984
-4.95 | 0.00595263
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
