thomasf10/cosy_cafeteria/powermeasurement/wifi/meting_all_sensorvalues_3.csv

#Digilent WaveForms Oscilloscope Acquisition
#Device Name: Discovery2
#Serial Number: SN:210321A4216E
#Date Time: 2020-04-24 14:15:11.596
#Sample rate: 800Hz
#Samples: 8000
#Trigger: Source: Channel 1 Type: Edge Condition: Rising Level: 0 V Hyst.: Auto HoldOff: 0 s
#Channel 1: Range: 50 mV/div Offset: -200 mV
Time (s) | Channel 1 (V)
-1.5 | 0.00161325
-1.49875 | 0.00394984
-1.4975 | 0.00461744
-1.49625 | 0.00361604
-1.495 | 0.00328224
-1.49375 | 0.00294844
-1.4925 | 0.00428364
-1.49125 | 0.00628643
-1.49 | 0.00461744
-1.48875 | 0.00228084
-1.4875 | 0.00161325
-1.48625 | 0.00228084
-1.485 | 0.00294844
-1.48375 | 0.00261464
-1.4825 | 0.000611848
-1.48125 | 0.000945647
-1.48 | 0.00161325
-1.47875 | 0.00394984
-1.4775 | 0.00461744
-1.47625 | 0.00361604
-1.475 | 0.00328224
-1.47375 | 0.00294844
-1.4725 | 0.00428364
-1.47125 | 0.00628643
-1.47 | 0.00461744
-1.46875 | 0.00261464
-1.4675 | 0.00161325
-1.46625 | 0.00228084
-1.465 | 0.00328224
-1.46375 | 0.00261464
-1.4625 | 0.000611848
-1.46125 | 0.000945647
-1.46 | 0.00161325
-1.45875 | 0.00361604
-1.4575 | 0.00461744
-1.45625 | 0.00361604
-1.455 | 0.00328224
-1.45375 | 0.00294844
-1.4525 | 0.00428364
-1.45125 | 0.00628643
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
