thomasf10/cosy_cafeteria/Report/fig/statendiagram.pdf

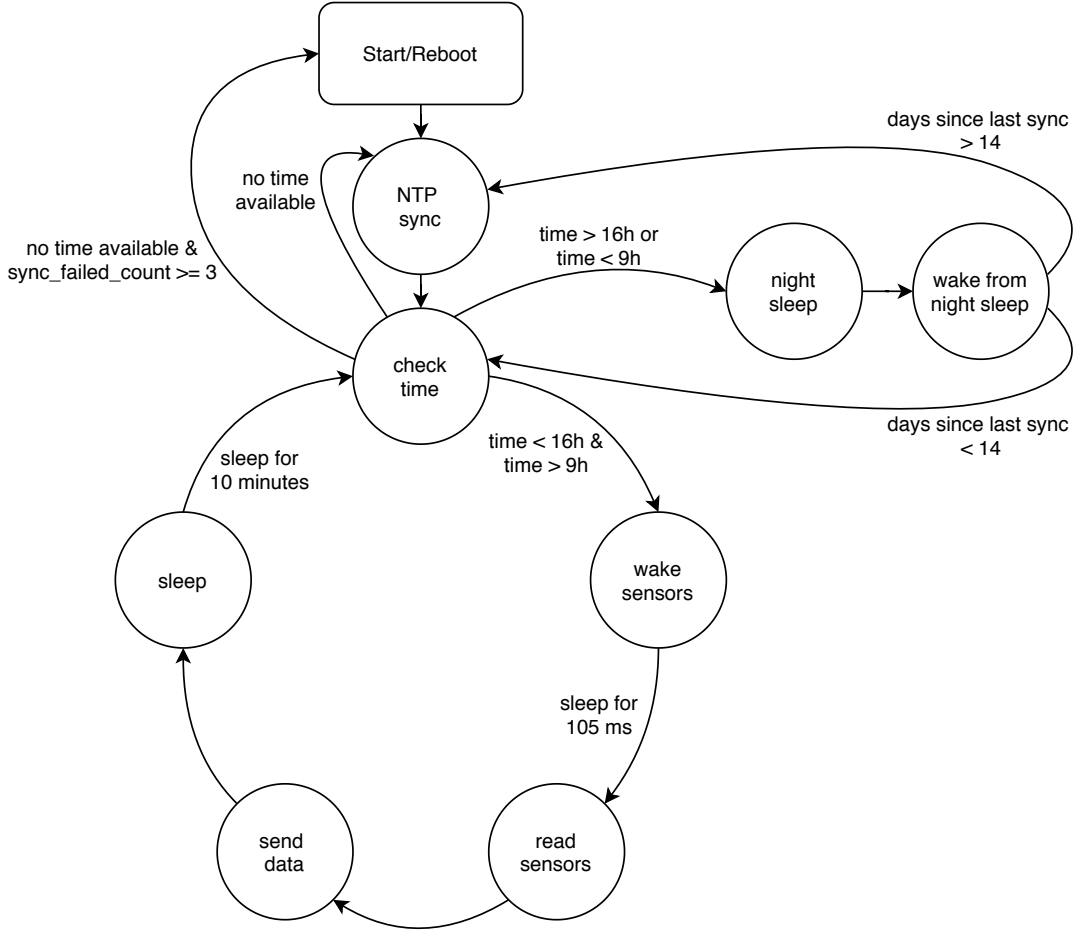
[picture p123: page 1]
Start/Reboot; check time; wake sensors; read sensors; send data; sleep; night sleep; wake from night sleep; NTP sync; sleep for 105 ms; time < 16h & time > 9h; time > 16h or time < 9h; sleep for 10 minutes; no time available

days since last sync

no time available &
sync_failed_count >= 3
