thomasf10/cosy_cafeteria/Report/fig/MainPCB_schematic.pdf

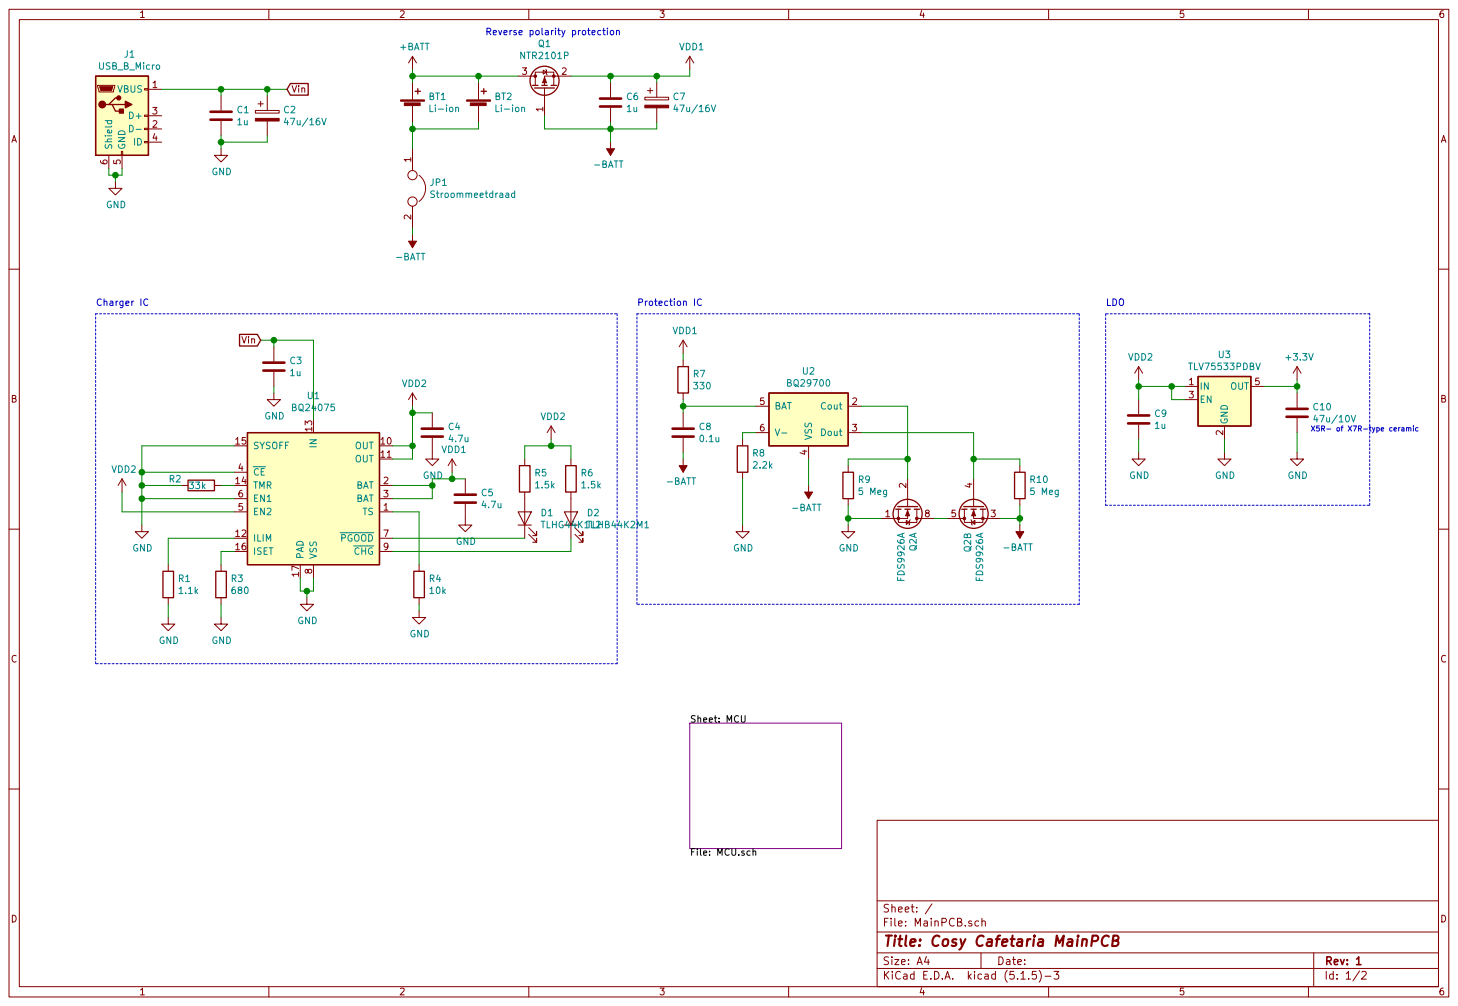
[picture p124: page 1]

File: MainPCB.sch Sheet: / Sheet: MCU

Id: 1/2 Title: Cosy Cafetaria MainPCB

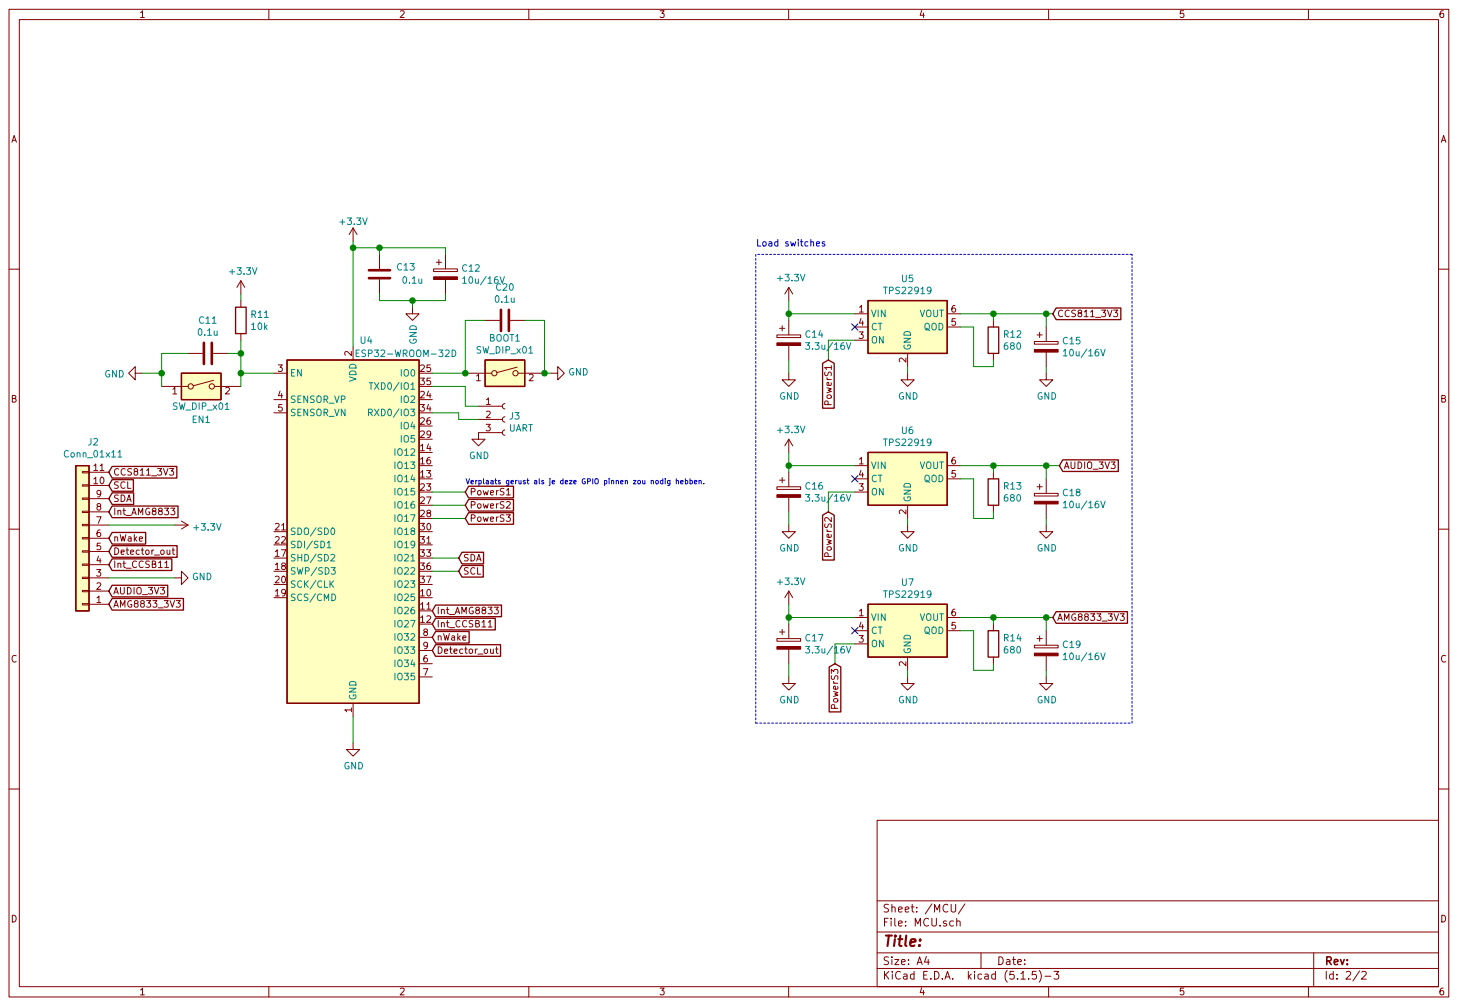
[picture p125: page 2]

2 ON 3 CT 4 QOD 5 VOUT 6 U5 TPS22919 GND

2 SCK/CLK 20 SDO/SD0 21 SDI/SD1 22

2 ON 3 CT 4 QOD 5 VOUT 6 U6 TPS22919 GND

2 ON 3 CT 4 QOD 5 VOUT 6 U7 TPS22919 GND

Id: 2/2 Title: File: MCU.sch Sheet: /MCU/
