thomasf10/cosy_cafeteria/Report/fig/architecture.pdf

### CPU BOARD

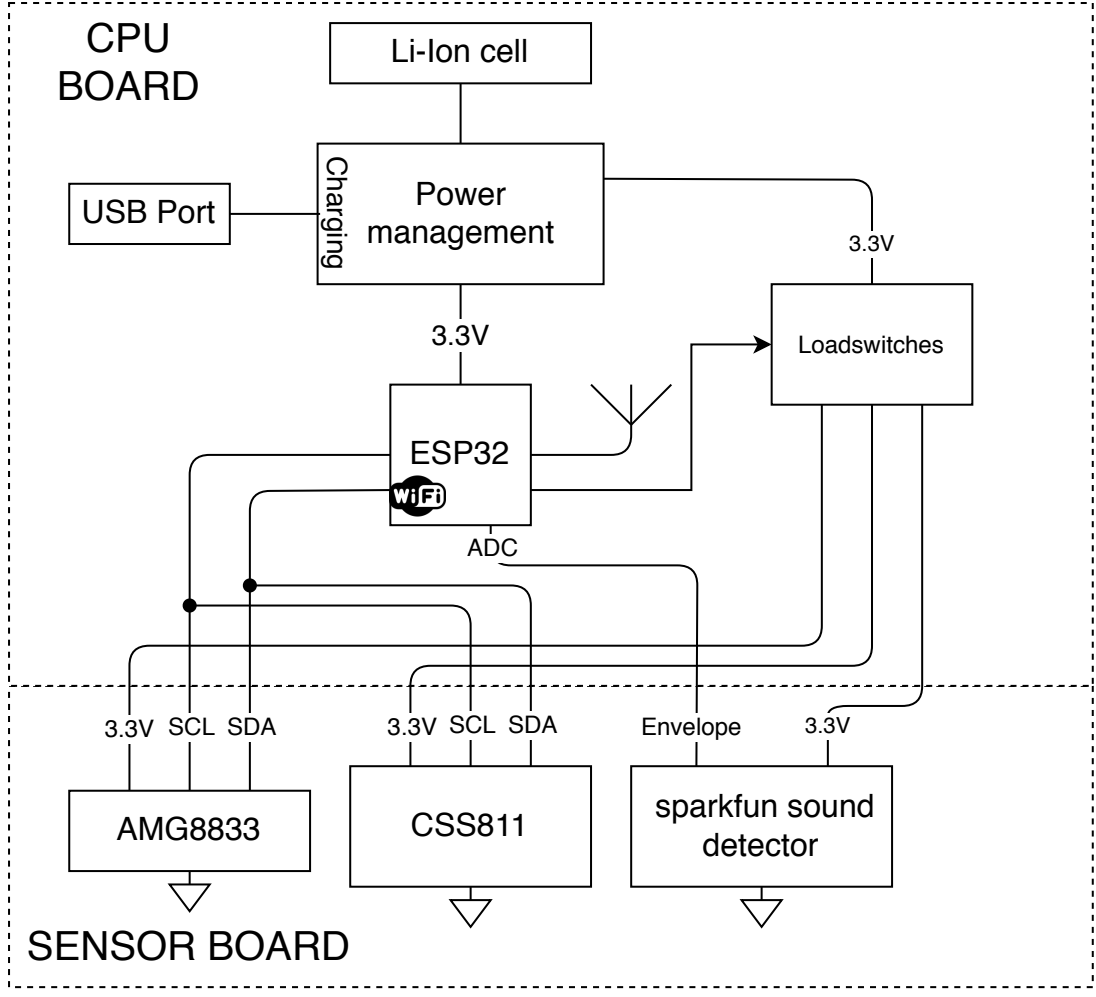
[picture p126: page 1]
Power; management USB Port; Charging; ESP32; AMG8833; SCL; SDA; sparkfun sound detector; Envelope; ADC; CSS811; SENSOR BOARD; Loadswitches

Li-Ion cell
