thomasf10/cosy_cafeteria/Hardware/SesnorBoard/SesnorBoard.pdf

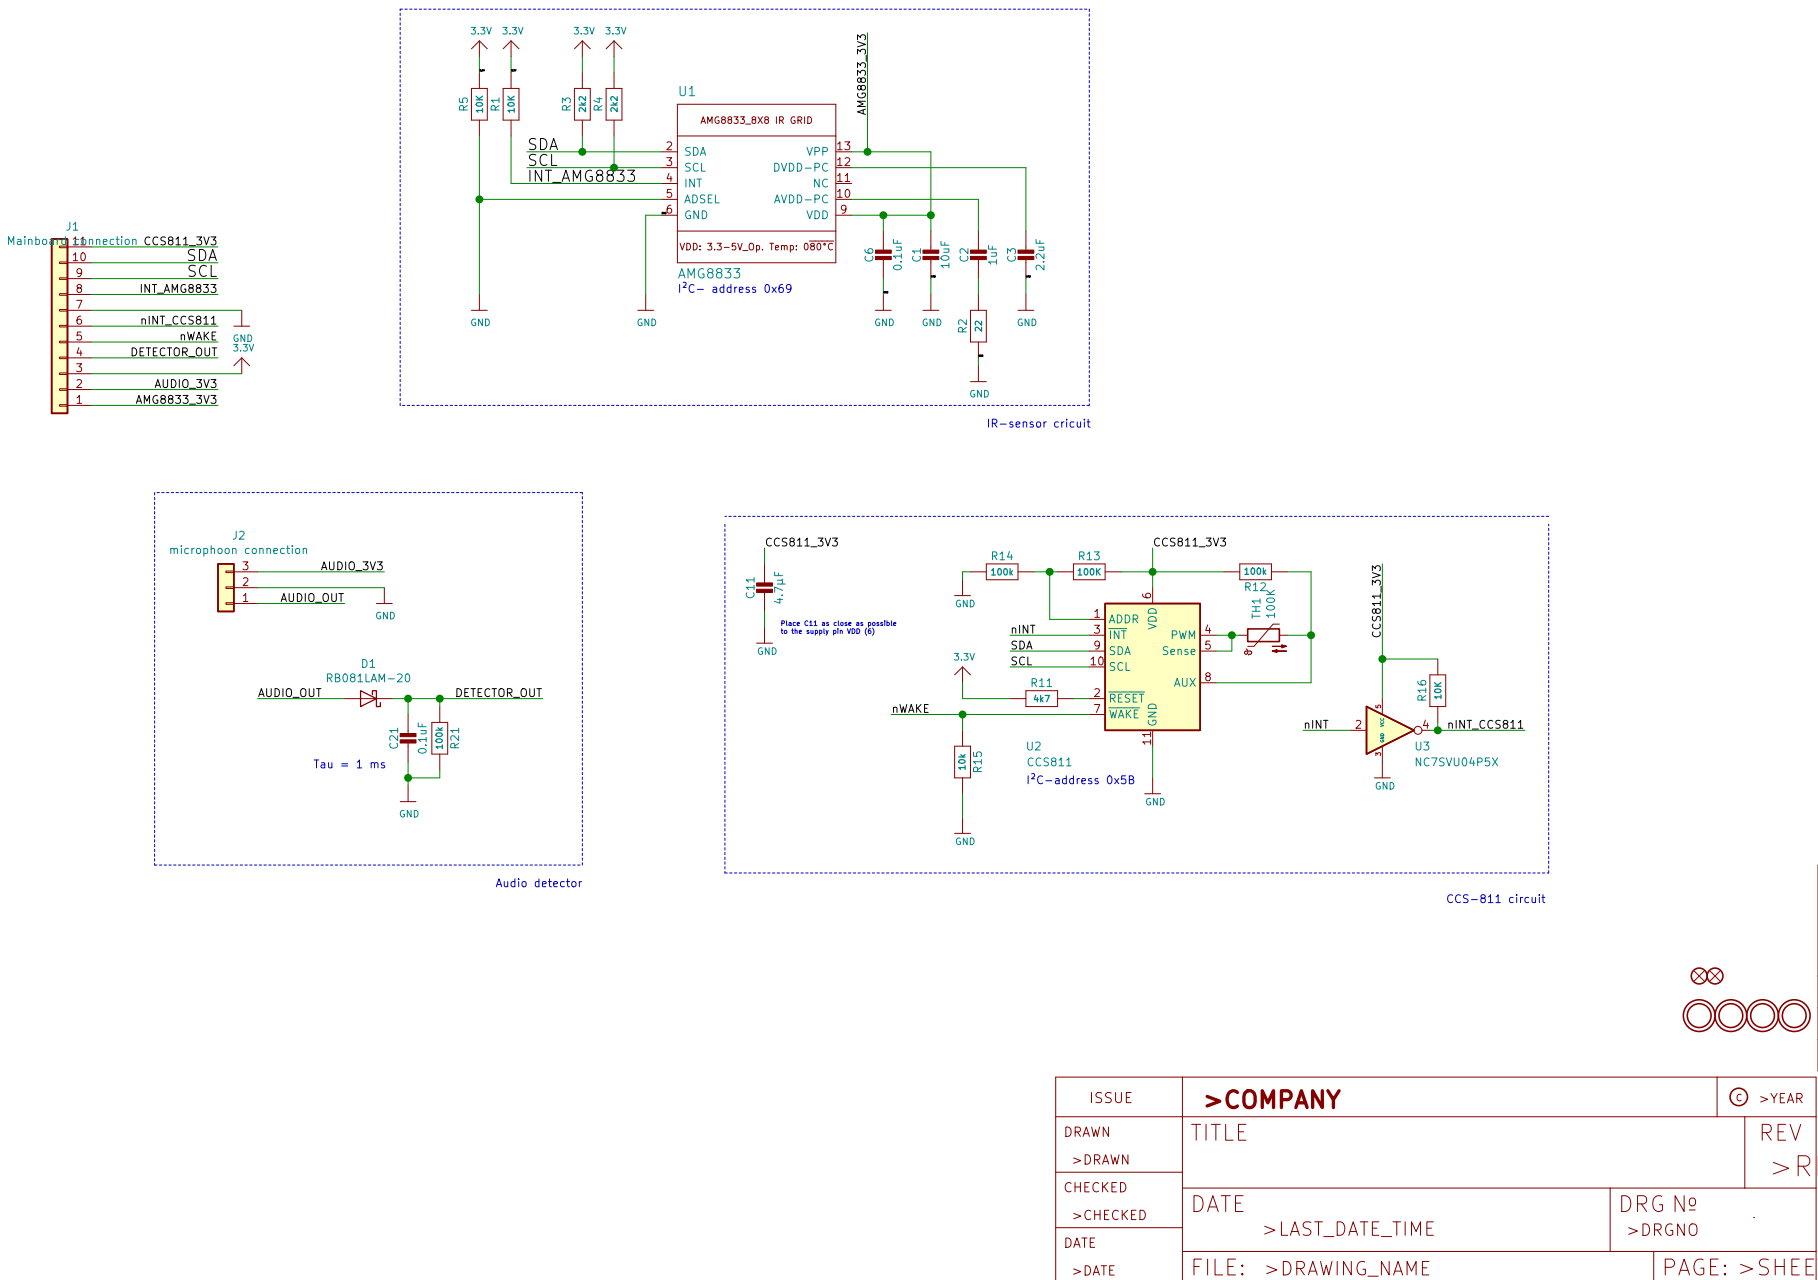
[picture p127: page 1]

100k R21 GND GND C6 0.1uF GND R5 10K R1 10K GND GND GND R222 C3 2.2uF C1 10uF C2 1uF R14

GND GND Place C11 as close as possible

to the supply pin VDD (6)

DRAWN | DRG

No PAGE:
