thomasf10/cosy_cafeteria/powermeasurement/wifi/NO_static_ip_64ints.pdf

## Verbruik = 0.043 mAh

## Verbruik

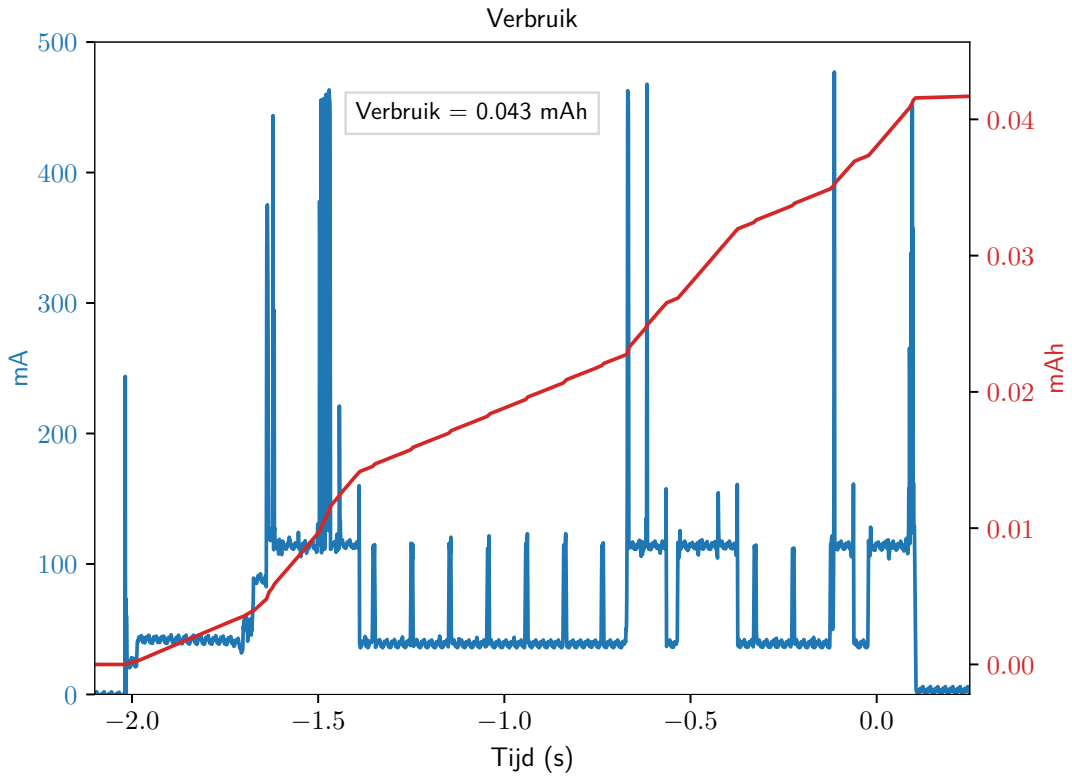
[picture p128: page 1]
Tijd (s); mAh
