thomasf10/cosy_cafeteria/powermeasurement/wifi/NO_static_ip_64ints_2e_meting.pdf

## Verbruik = 0.033 mAh

## Verbruik

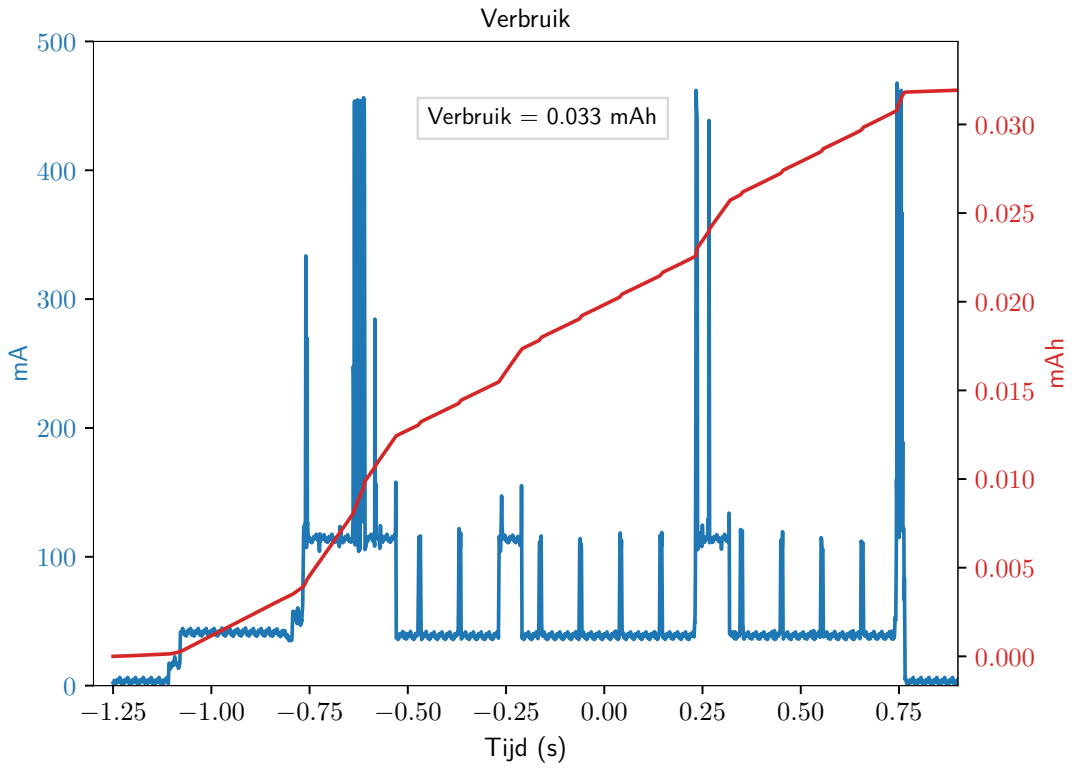
[picture p129: page 1]
Tijd (s); mAh
