thomasf10/cosy_cafeteria/powermeasurement/wifi/static_ip_64ints.pdf

## Verbruik = 0.046 mAh

## Verbruik

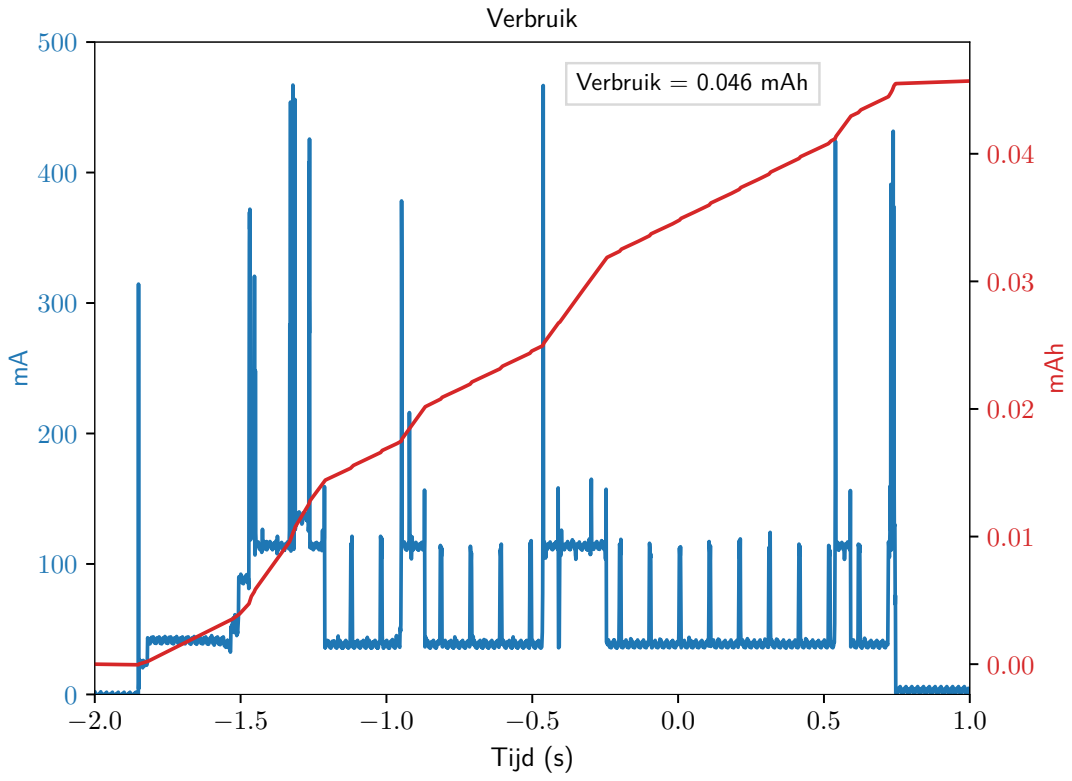
[picture p130: page 1]
Tijd (s); mAh
