thomasf10/cosy_cafeteria/powermeasurement/wifi/static_ip_64ints_2e_meting.pdf

## Verbruik = 0.047 mAh

## Verbruik

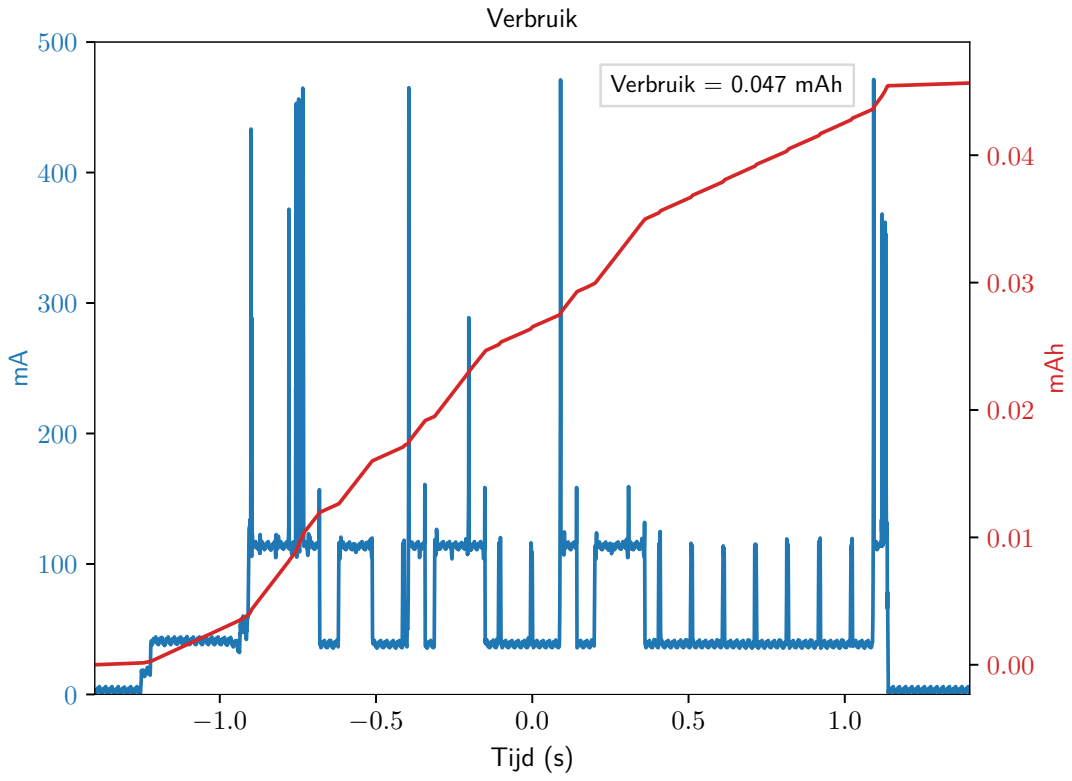
[picture p131: page 1]
Tijd (s); mAh
