thomasf10/cosy_cafeteria/Report/fig/wifi_pwr.pdf

## Verbruik = 0.041 mAh

## Verbruik

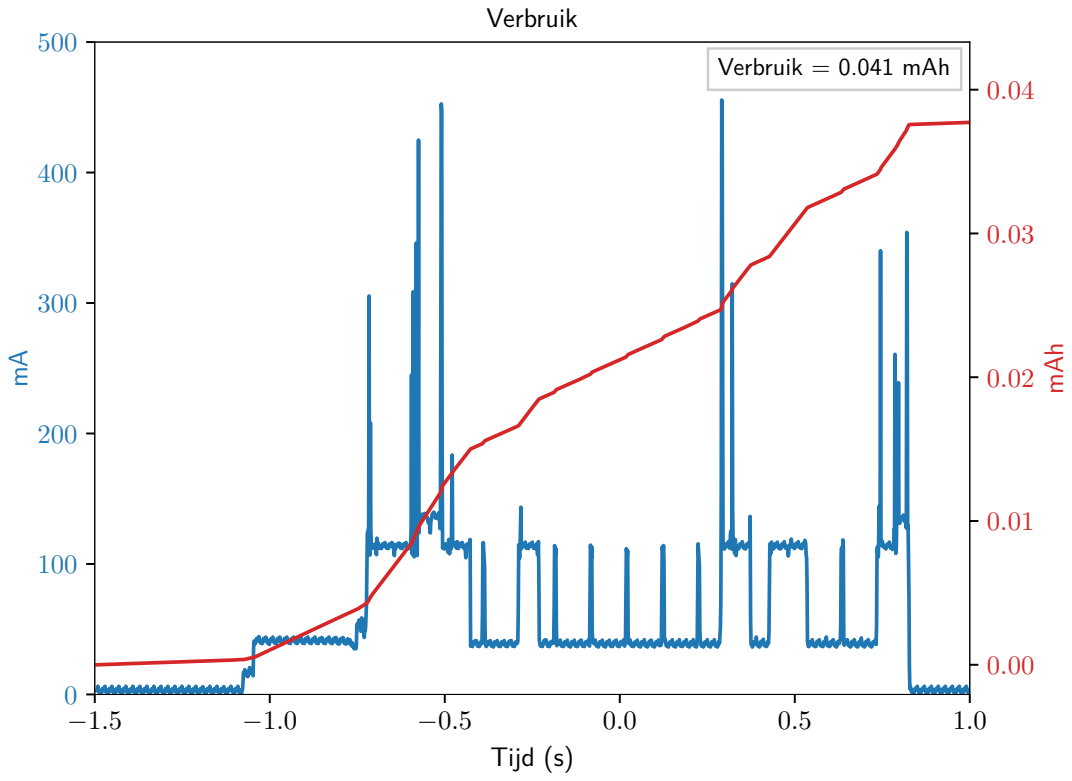
[picture p132: page 1]
Tijd (s); mAh
