thomasf10/cosy_cafeteria/Masterplan/fig/architecture.pdf

### CPU BOARD

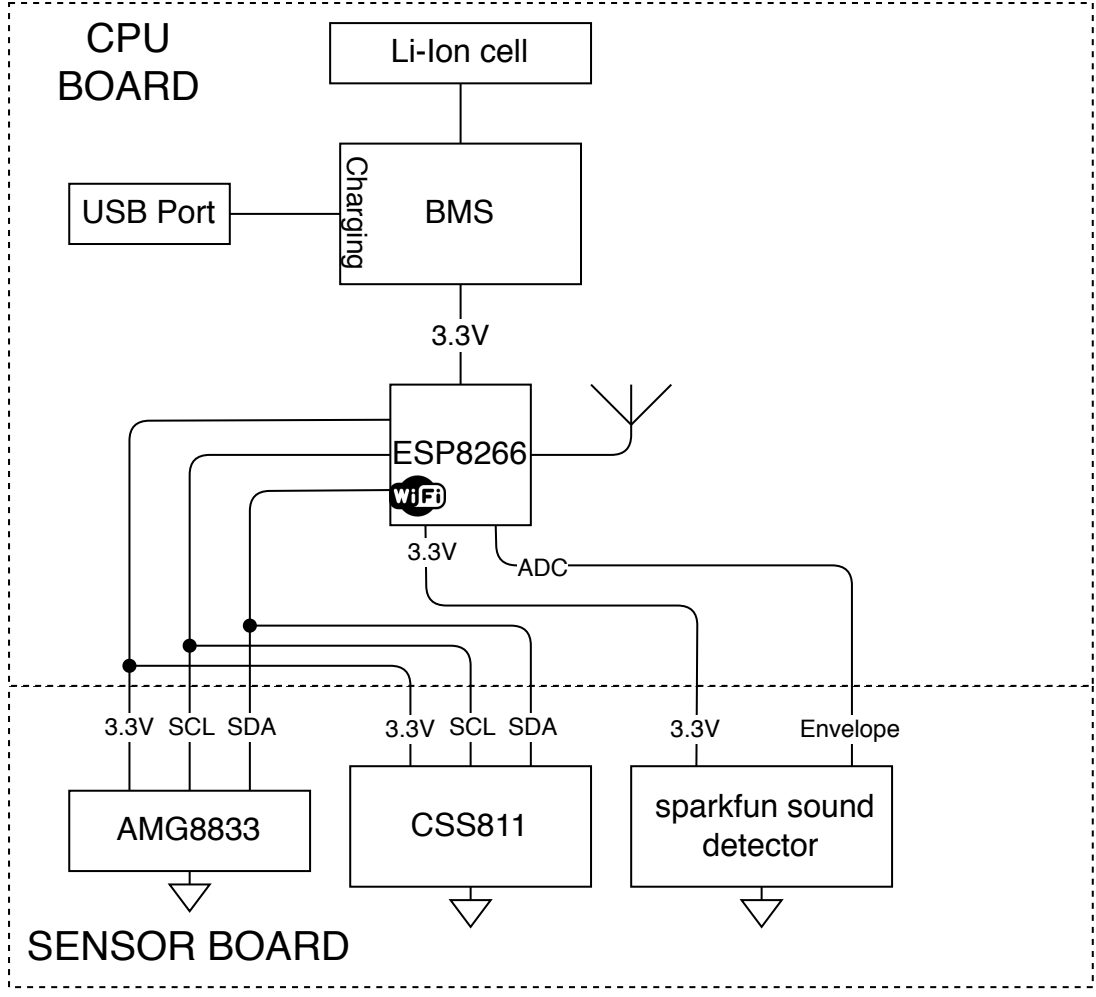
[picture p133: page 1]
USB Port; BMS Charging; ESP8266; AMG8833; SCL; SDA; sparkfun sound detector; Envelope; ADC; CSS811; SENSOR BOARD

Li-Ion cell
