thomasf10/cosy_cafeteria/Documentation/Power management design/Battery holder (1).PDF

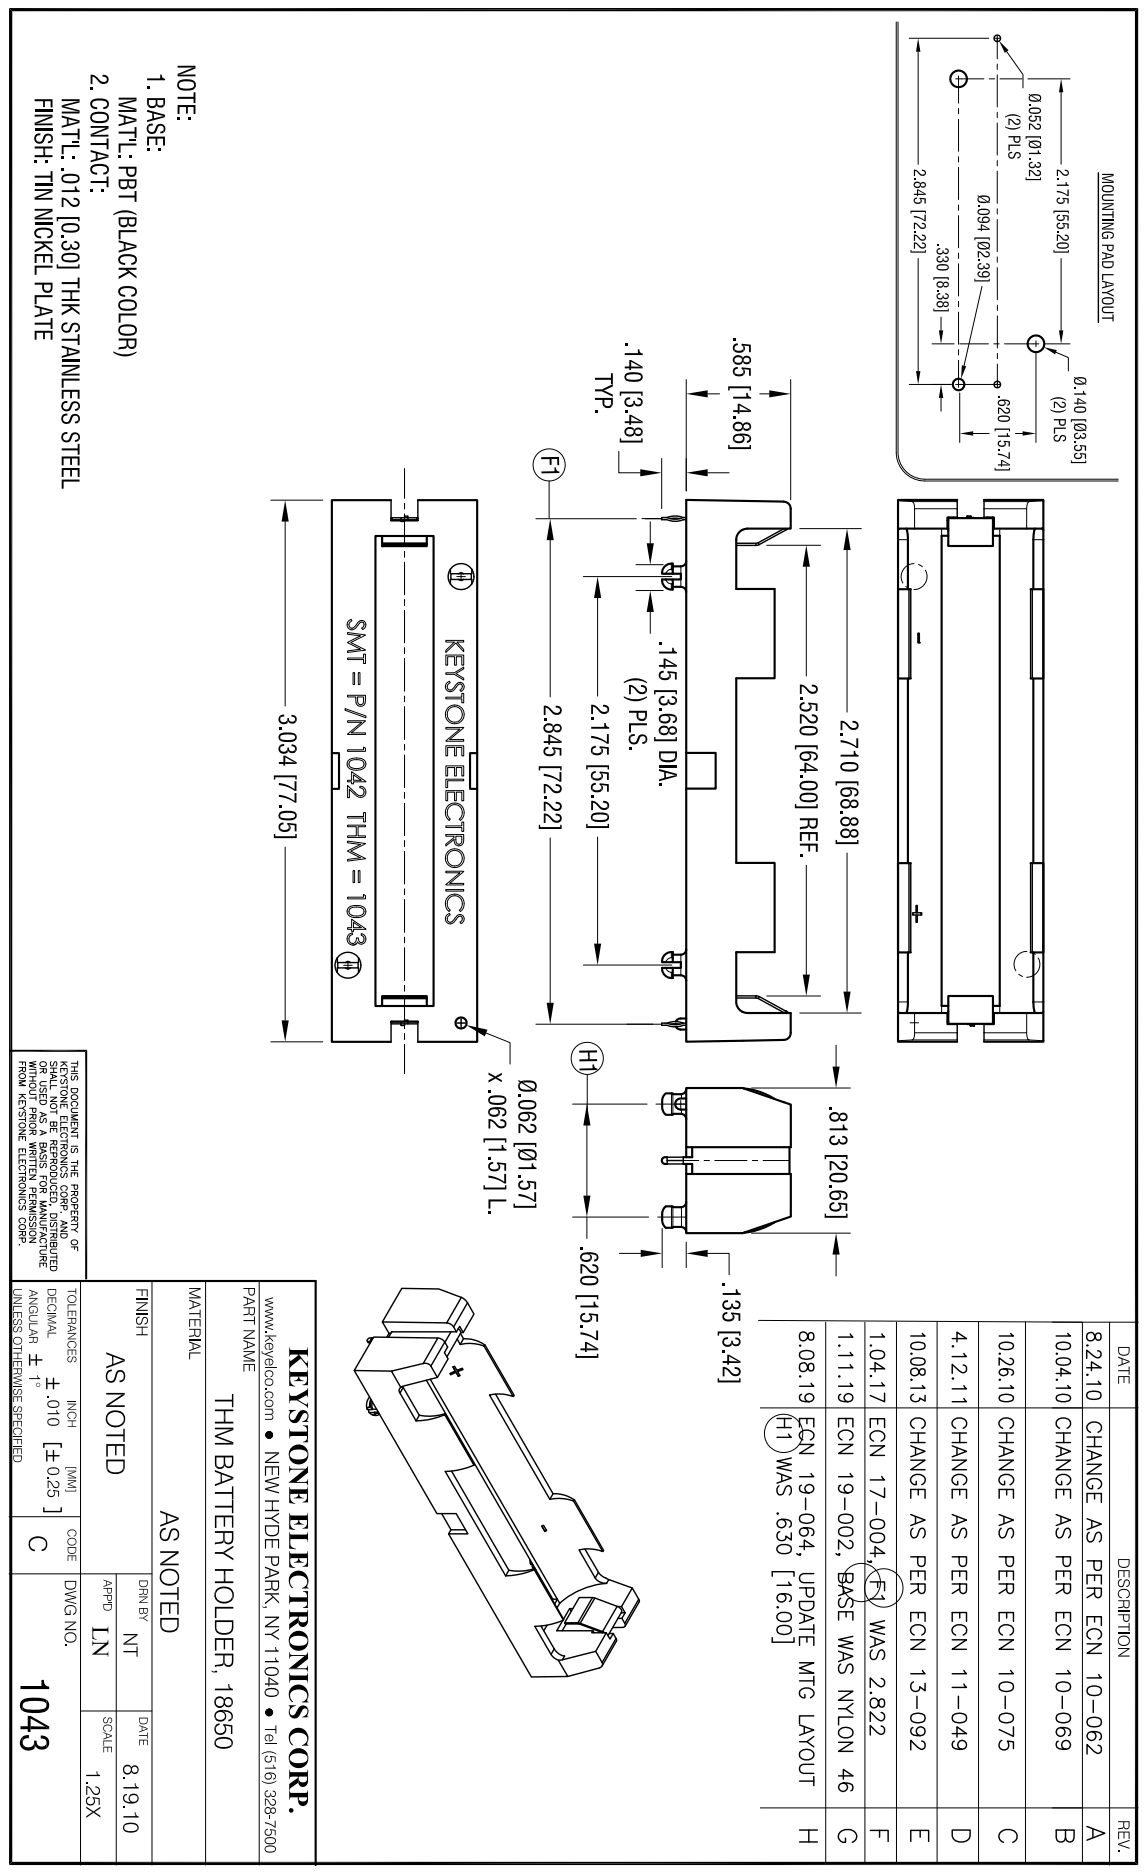
[picture p135: page 1]
