thomasf10/cosy_cafeteria/Report/fig/situation.pdf

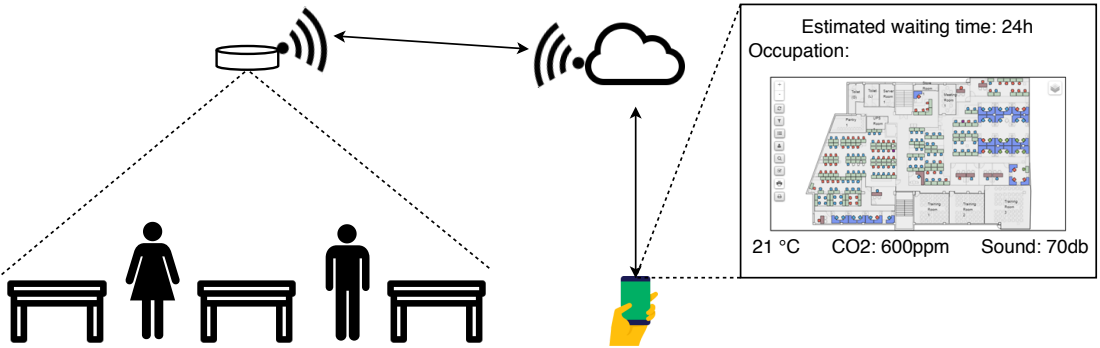
[picture p136: page 1]
CO2: 600ppm; Sound: 70db

Estimated waiting time: 24h
Occupation:
