thomasf10/cosy_cafeteria/Hardware/MainPCB/Gerbers/MainPCB-F_SilkS.pdf

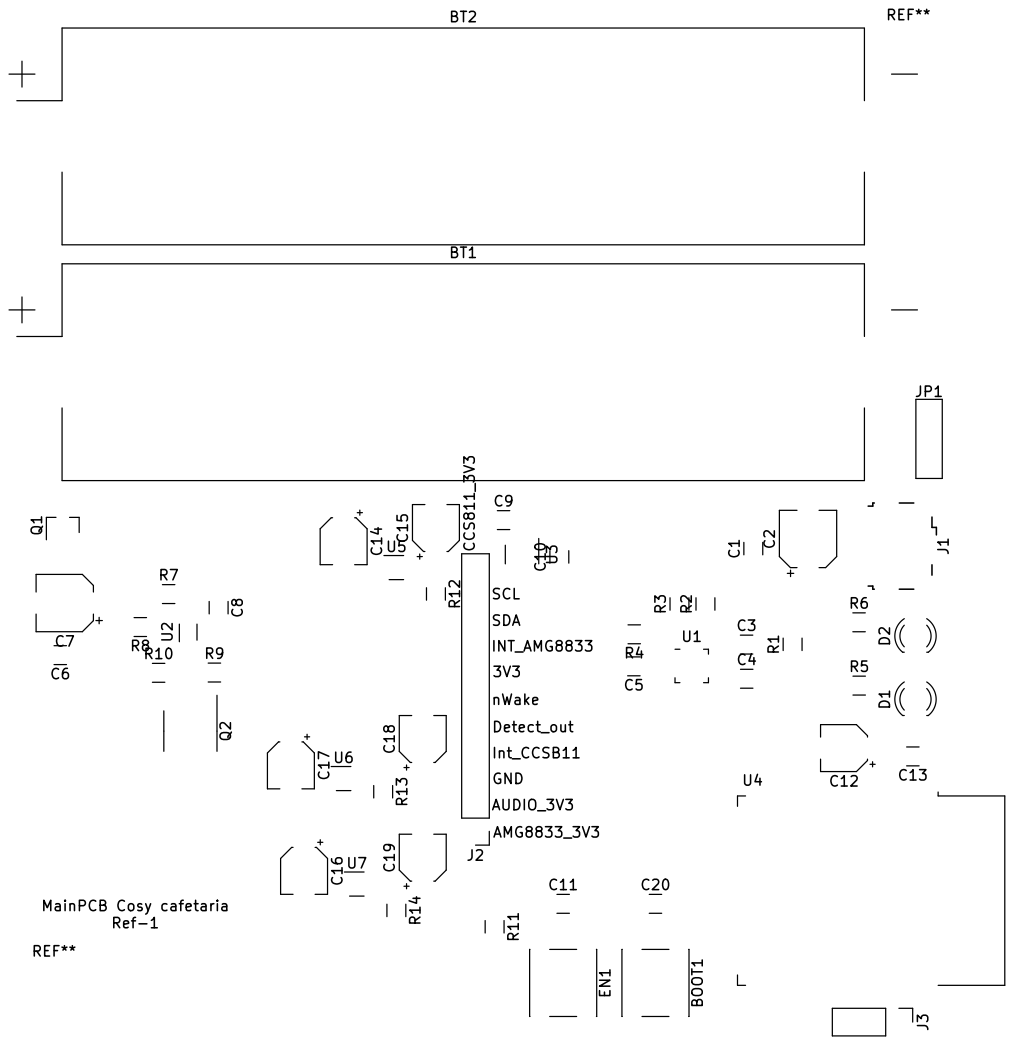
[picture p137: page 1]
