thomasf10/cosy_cafeteria/Dashboard/img/cafetaria (2).pdf

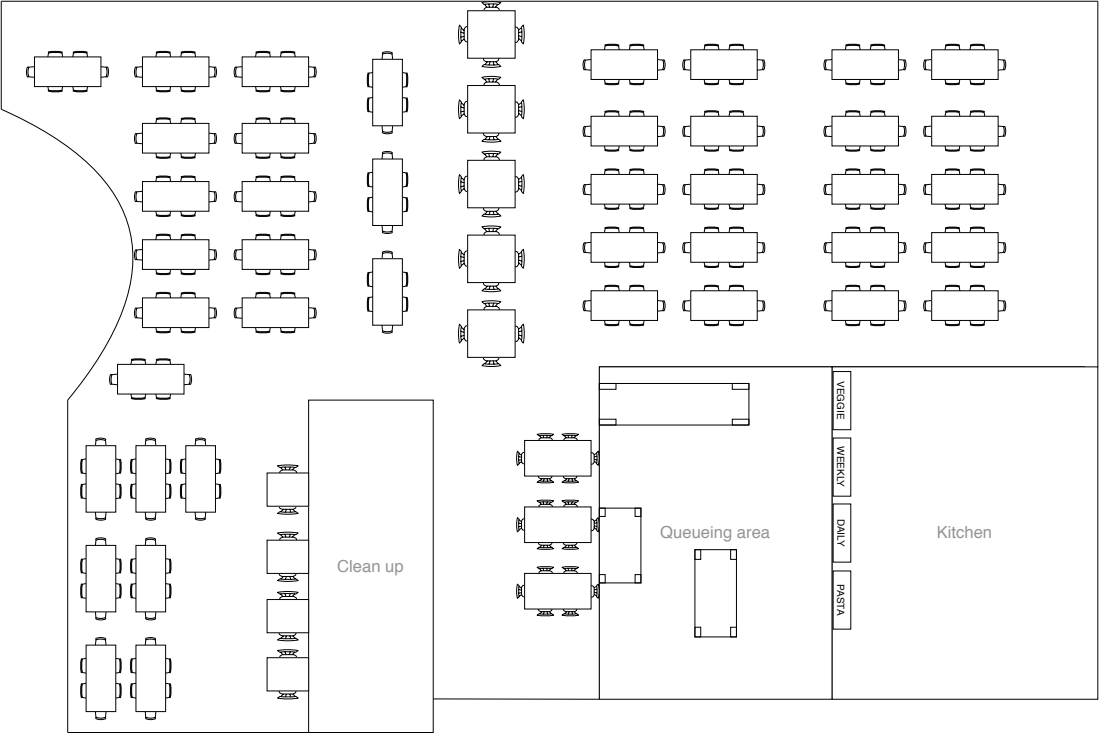
[picture p138: page 1]
Clean up; Queueing area; Kitchen PASTA DAILY VEGGIE WEEKLY
