thomasf10/cosy_cafeteria/Wi-Fi/metingen_stroomprobe/metstroomprobe/1e_meting2.pdf

## Verbruik

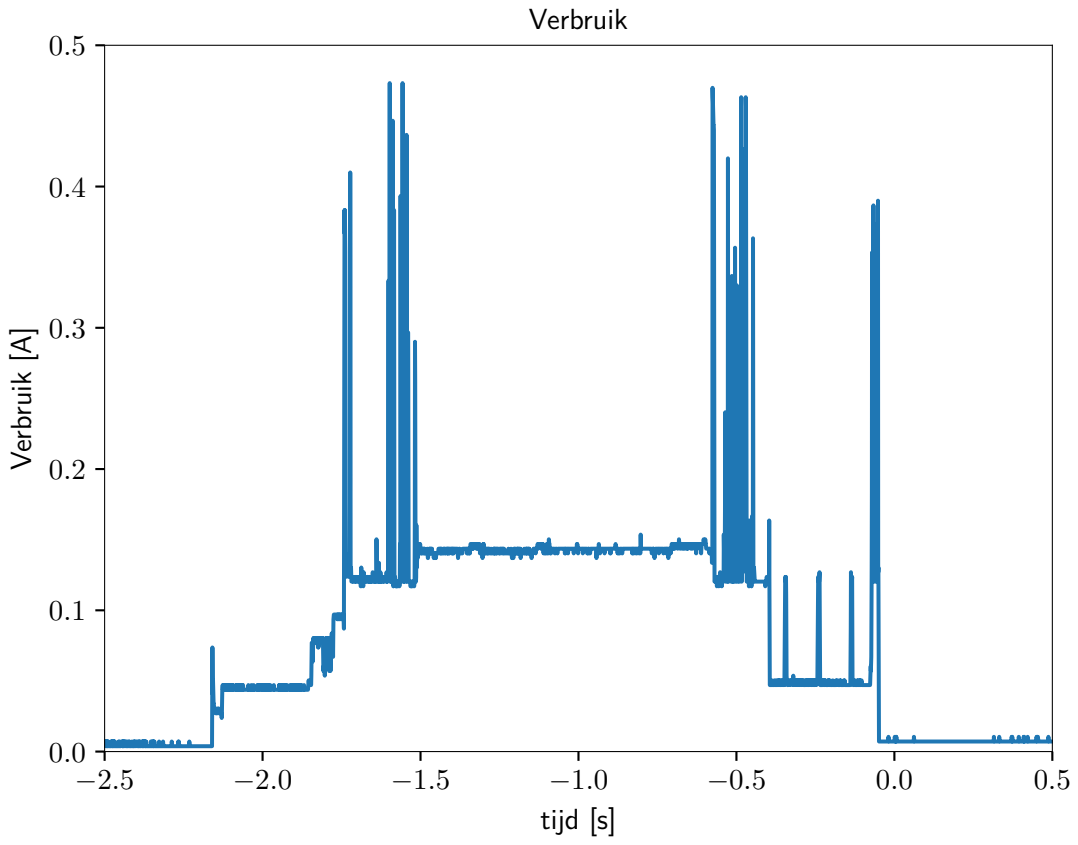
[picture p139: page 1]
tijd [s]; Verbruik [A]
