thomasf10/cosy_cafeteria/Wi-Fi/metingen_stroomprobe/metstroomprobe/1e_meting2_int.pdf

## Verbruik

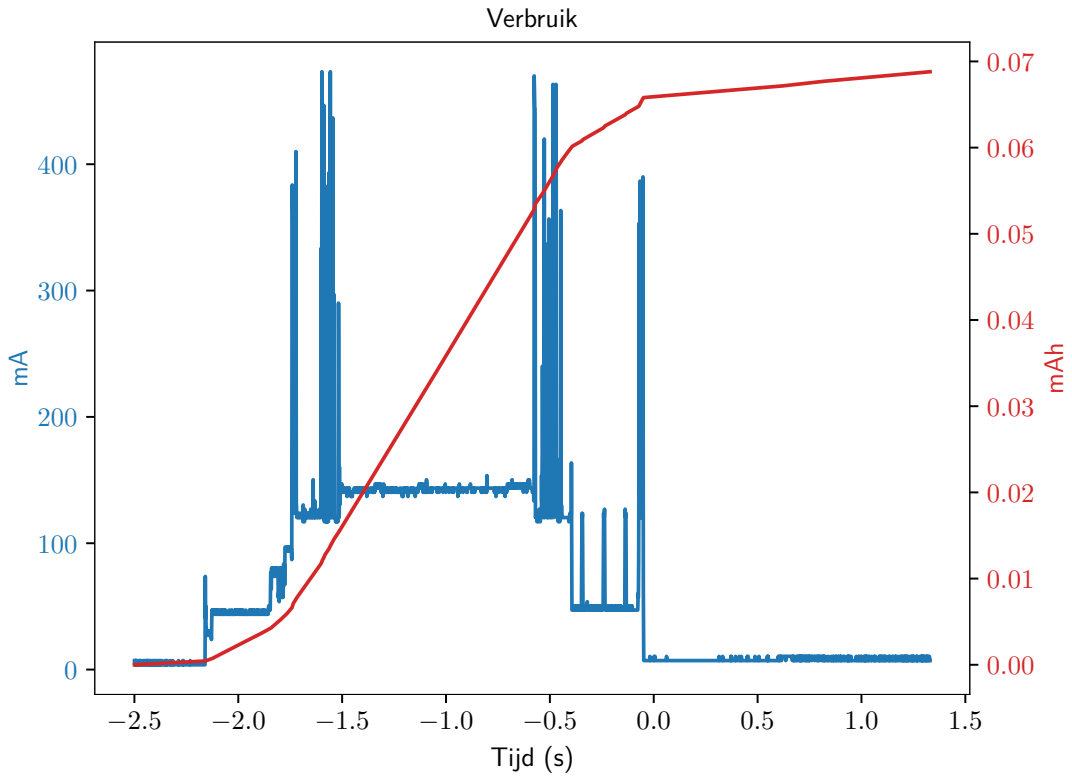
[picture p140: page 1]
Tijd (s); mAh
