thomasf10/cosy_cafeteria/Wi-Fi/metingen_stroomprobe/metstroomprobe/2e_meting2.pdf

## Verbruik

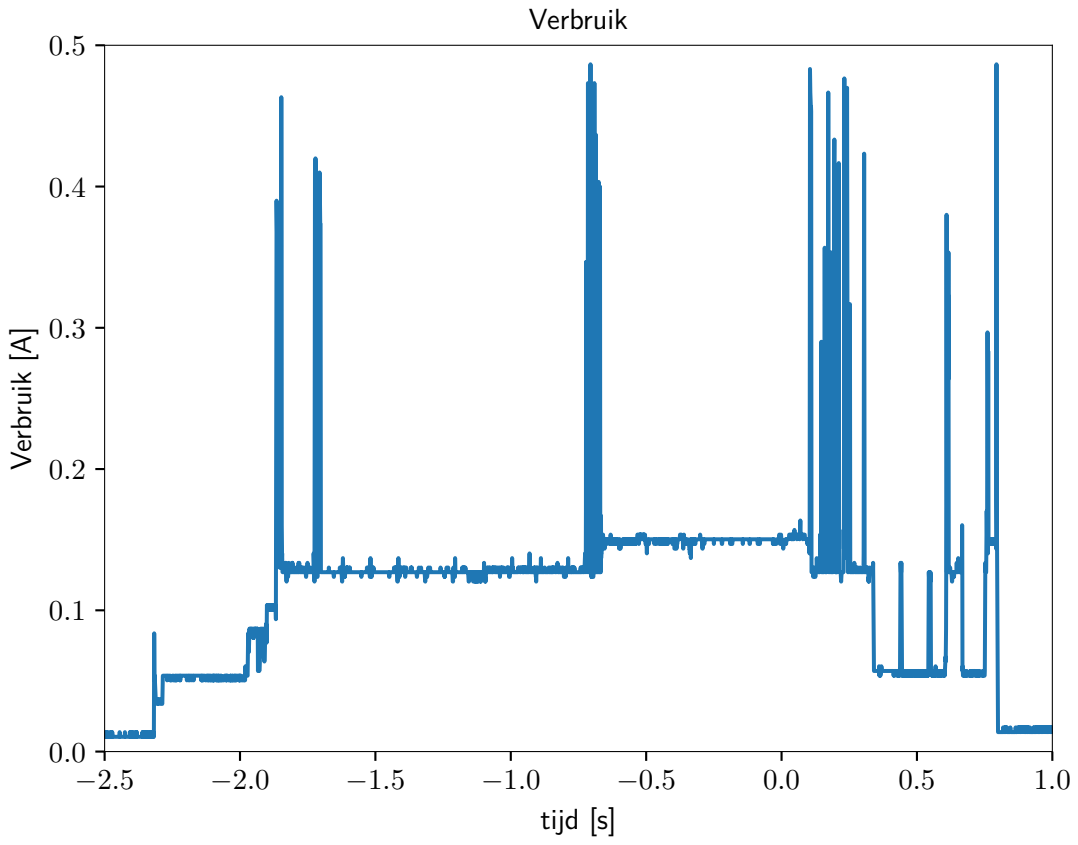
[picture p141: page 1]
tijd [s]; Verbruik [A]
