thomasf10/cosy_cafeteria/Wi-Fi/metingen_stroomprobe/metstroomprobe/2e_meting2_int.pdf

## Verbruik

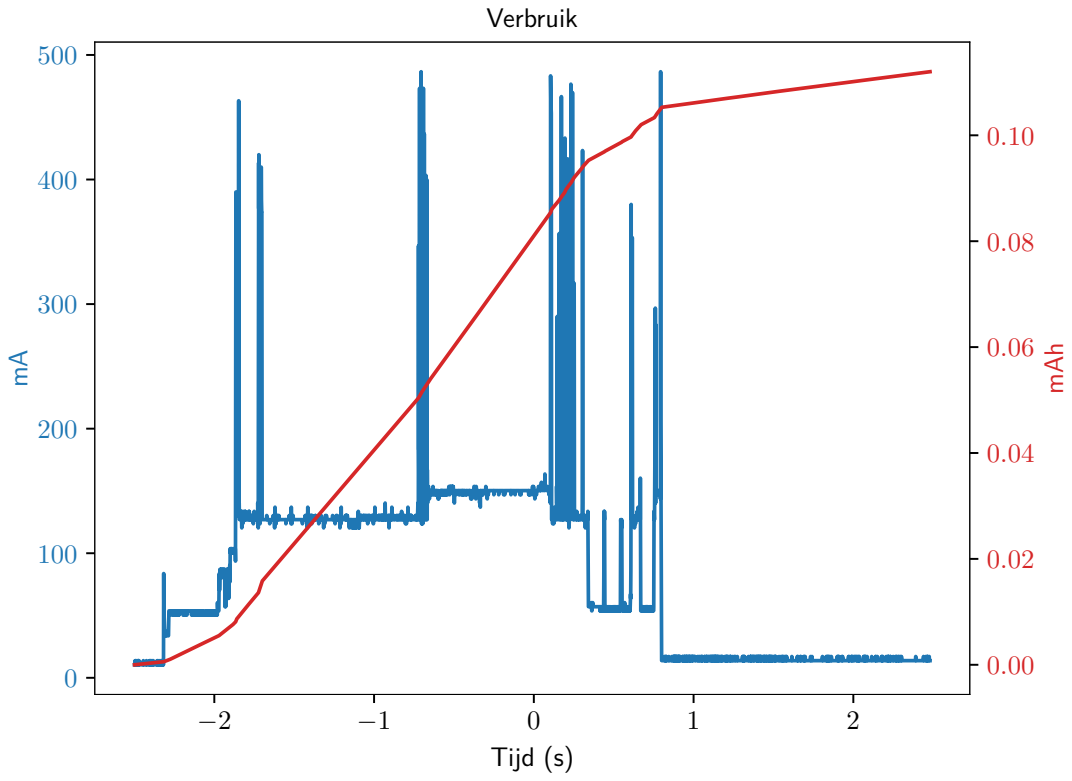
[picture p142: page 1]
Tijd (s); mAh
