thomasf10/cosy_cafeteria/Wi-Fi/metingen_stroomprobe/metstroomprobe/3e_meting.pdf

## Verbruik

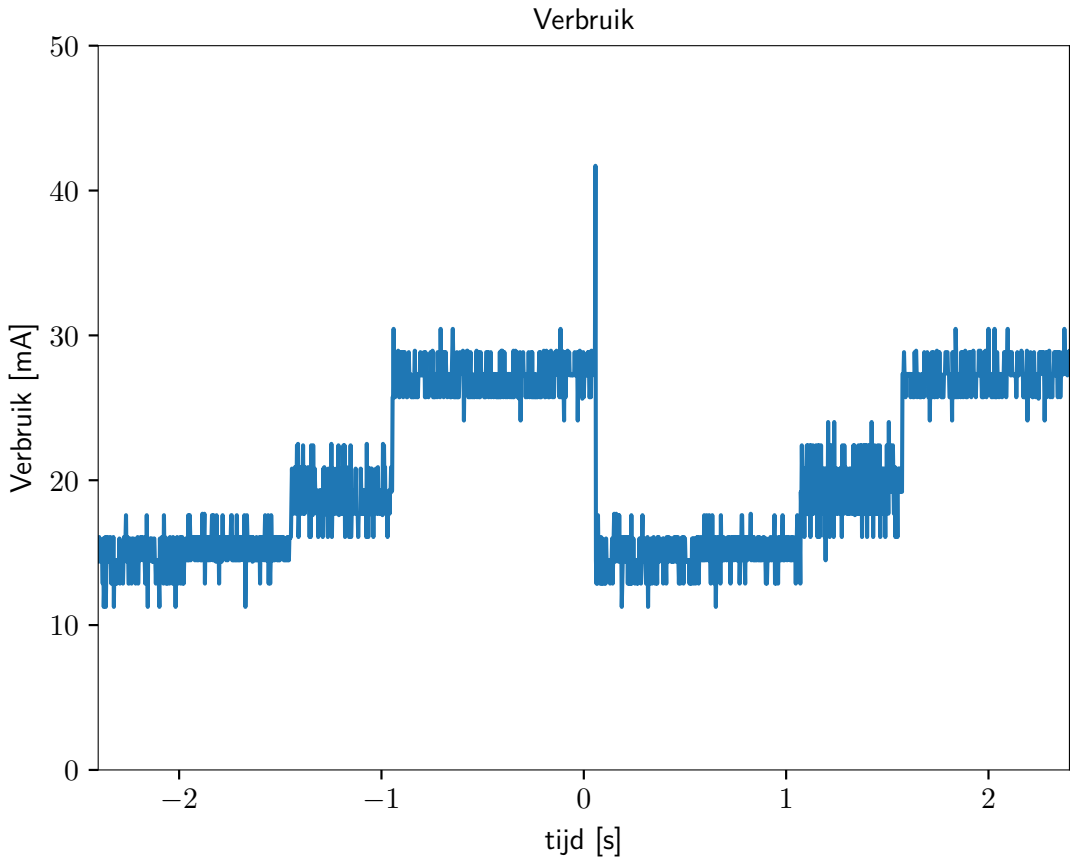
[picture p143: page 1]
tijd [s]; Verbruik [mA]
