thomasf10/cosy_cafeteria/Wi-Fi/metingen_stroomprobe/metstroomprobe/4e_meting.pdf

## Verbruik

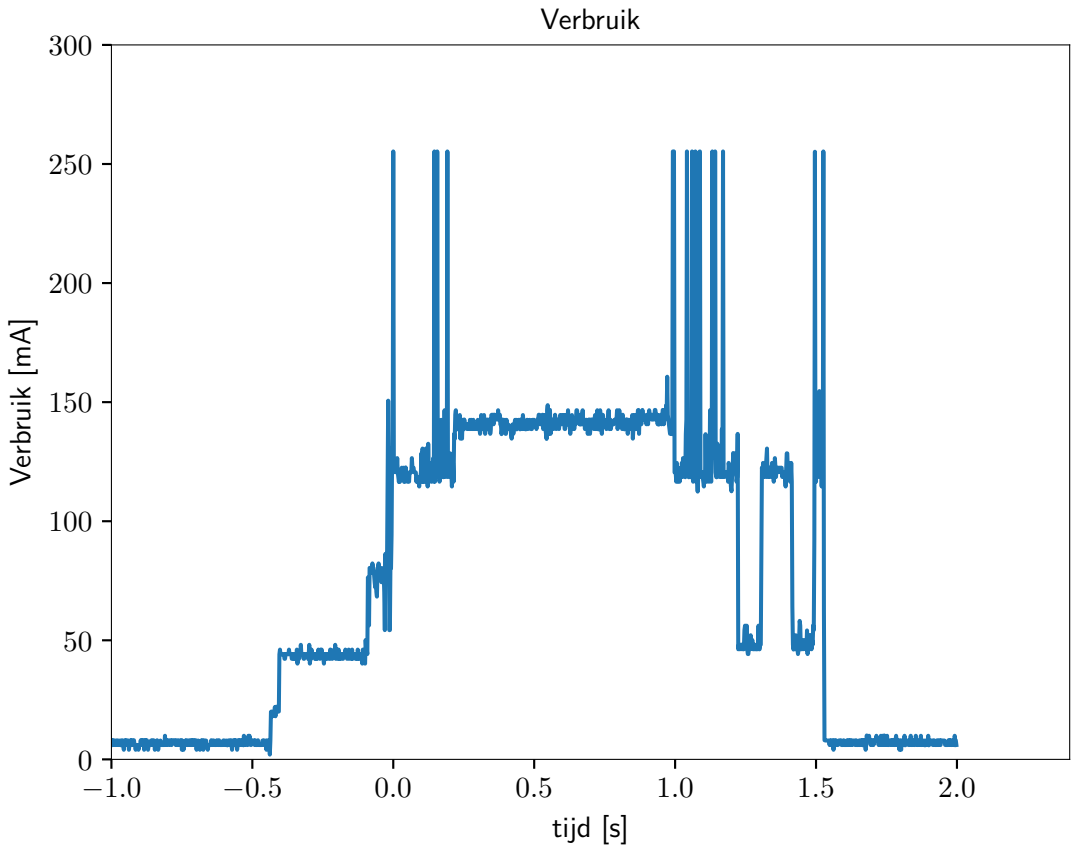
[picture p144: page 1]
tijd [s]; Verbruik [mA]
