thomasf10/cosy_cafeteria/Wi-Fi/metingen_stroomprobe/metstroomprobe/4e_meting2_int.pdf

## Verbruik

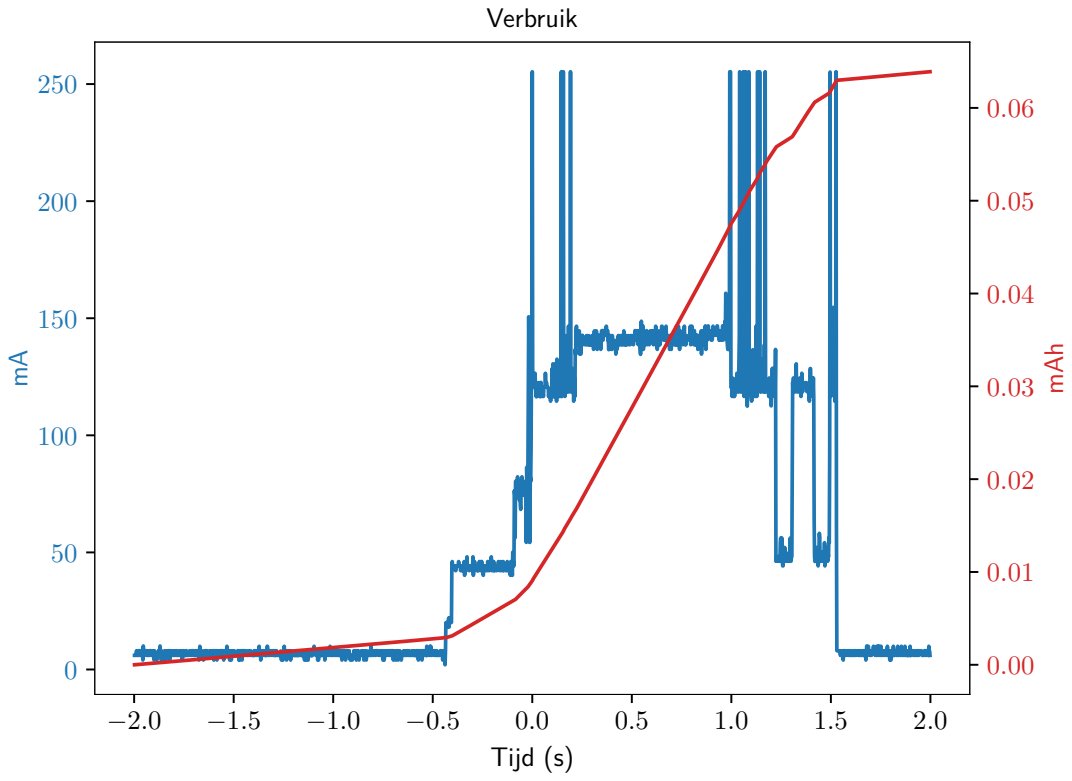
[picture p145: page 1]
Tijd (s); mAh
