thomasf10/cosy_cafeteria/Documentation/Power management design/Reverse polarity protection/Polarity_protection.asc

C1: cap; 10n
R2: res; 10k
U1: ntr2101pt1
V1: voltage; PULSE(0 4.2 0 10u 10u 100u)
Named nets: in, out, 0
.tran 0 300u 0
